MorseKOB/MuKOB/hw/renderings/MK-CommAdapter_1_0_b.png

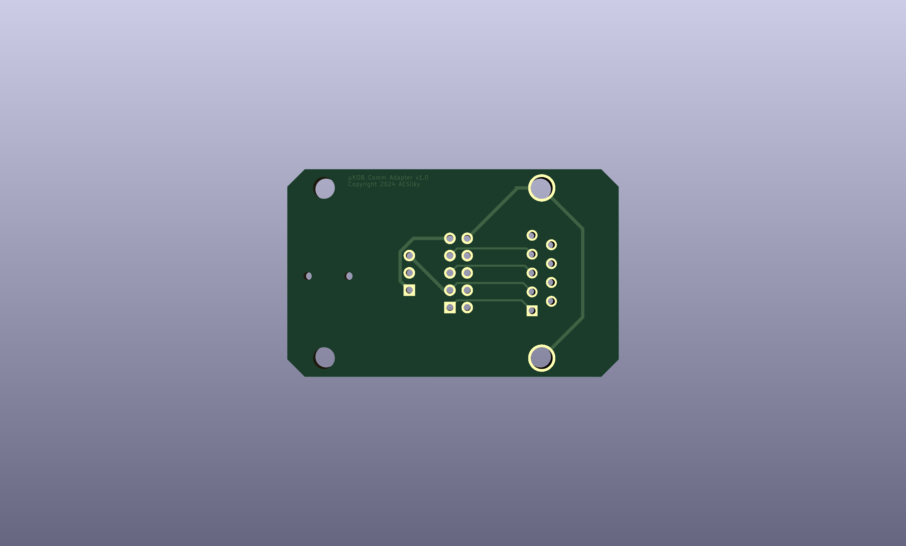
hw/renderings/MK-CommAdapter_1_0_b.png
