MorseKOB/MuKOB/hw/renderings/MK-JackAdapter-v1_1.png

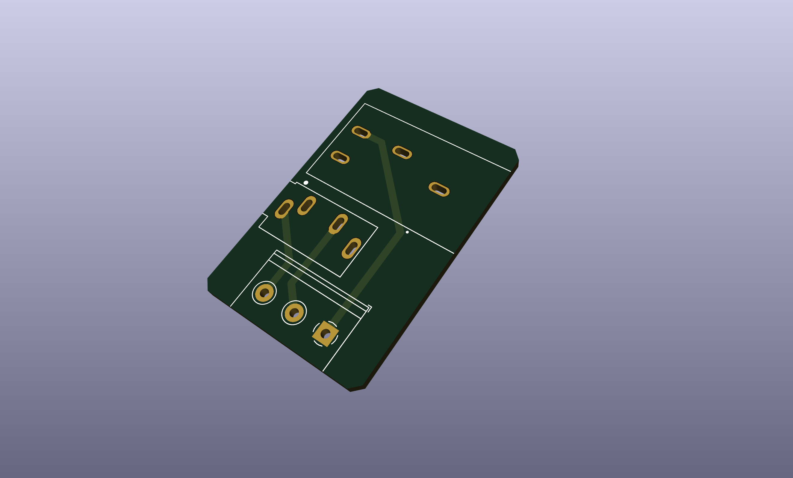
hw/renderings/MK-JackAdapter-v1_1.png
