MorseKOB/MuKOB/hw/renderings/MK-JackAdapter_1_0_b.png

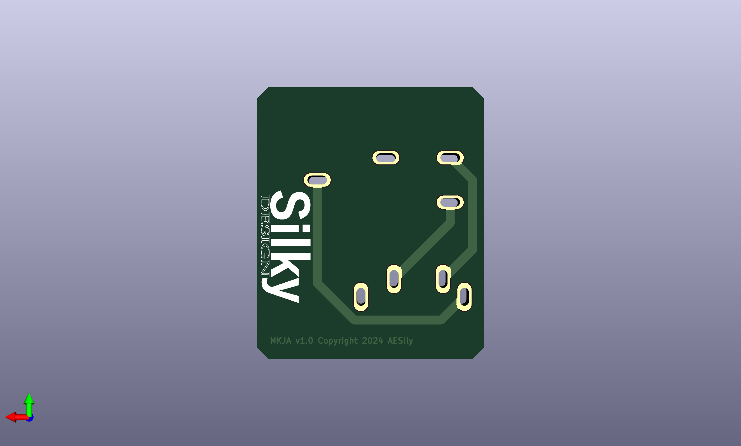
hw/renderings/MK-JackAdapter_1_0_b.png
