MorseKOB/MuKOB/hw/renderings/MK-KS-MkII_1_0_b.png

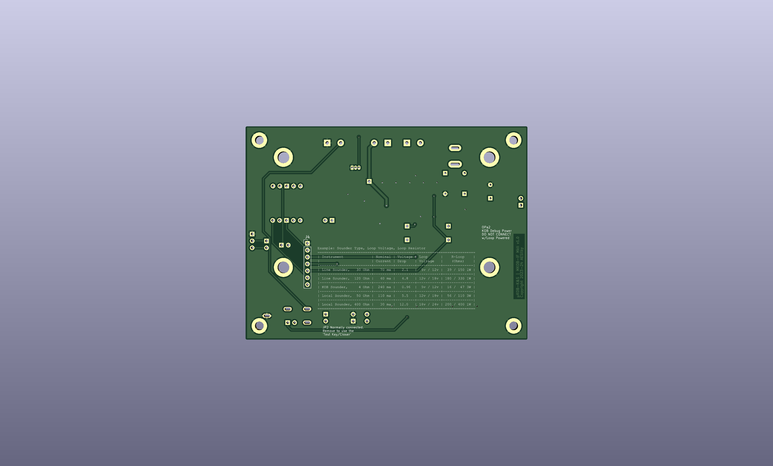
hw/renderings/MK-KS-MkII_1_0_b.png
