MorseKOB/MuKOB/hw/renderings/MuKOB_1_0_b.png

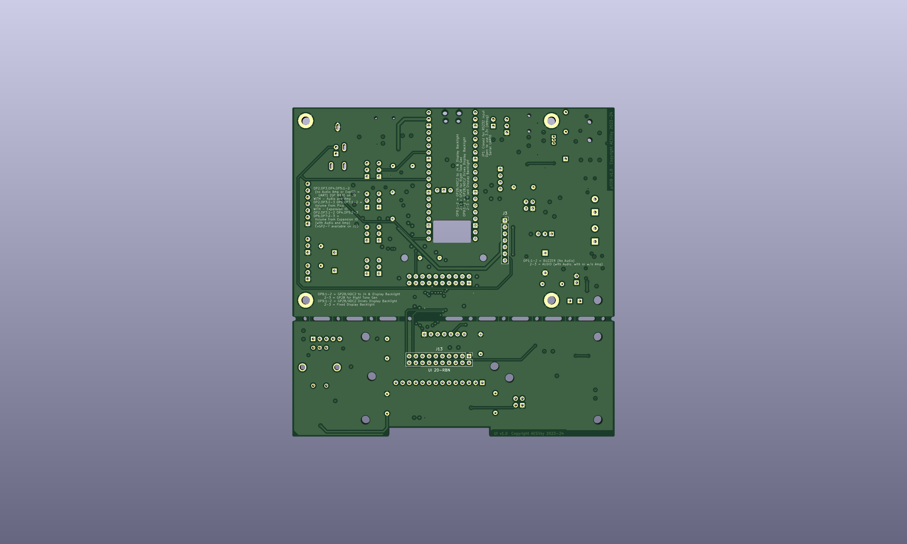
hw/renderings/MuKOB_1_0_b.png
