MorseKOB/MuKOB/hw/renderings/MuKOB_1_0_f.png

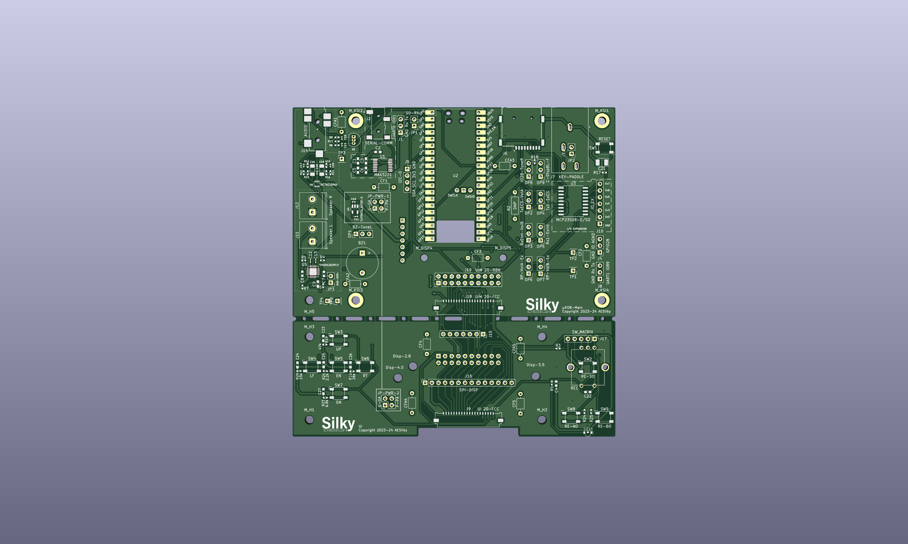
hw/renderings/MuKOB_1_0_f.png
