MorseKOB/MuKOB/component-docs/FFC_FPC-SOCK-Amphenol-F52R-mech.pdf

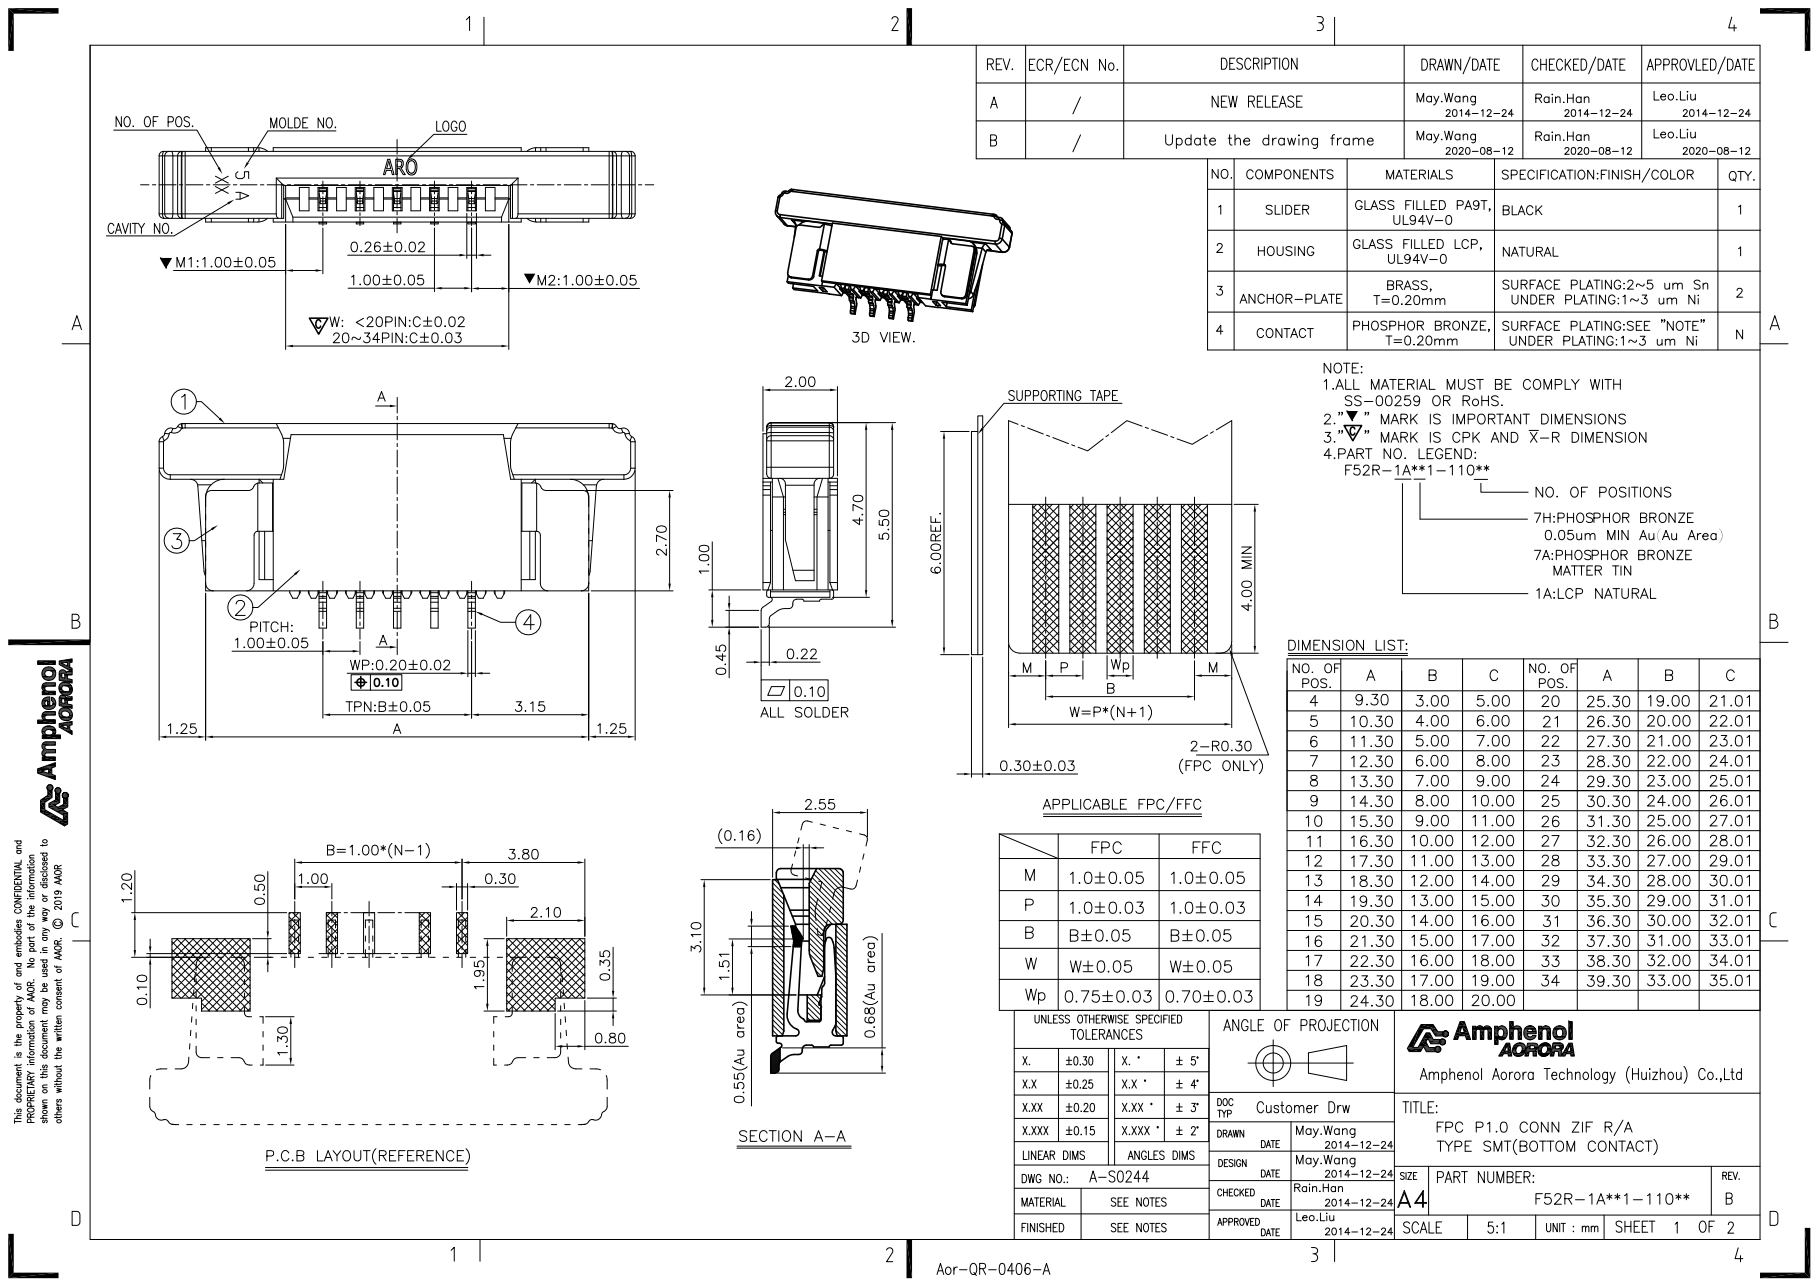
[picture p38: page 1]

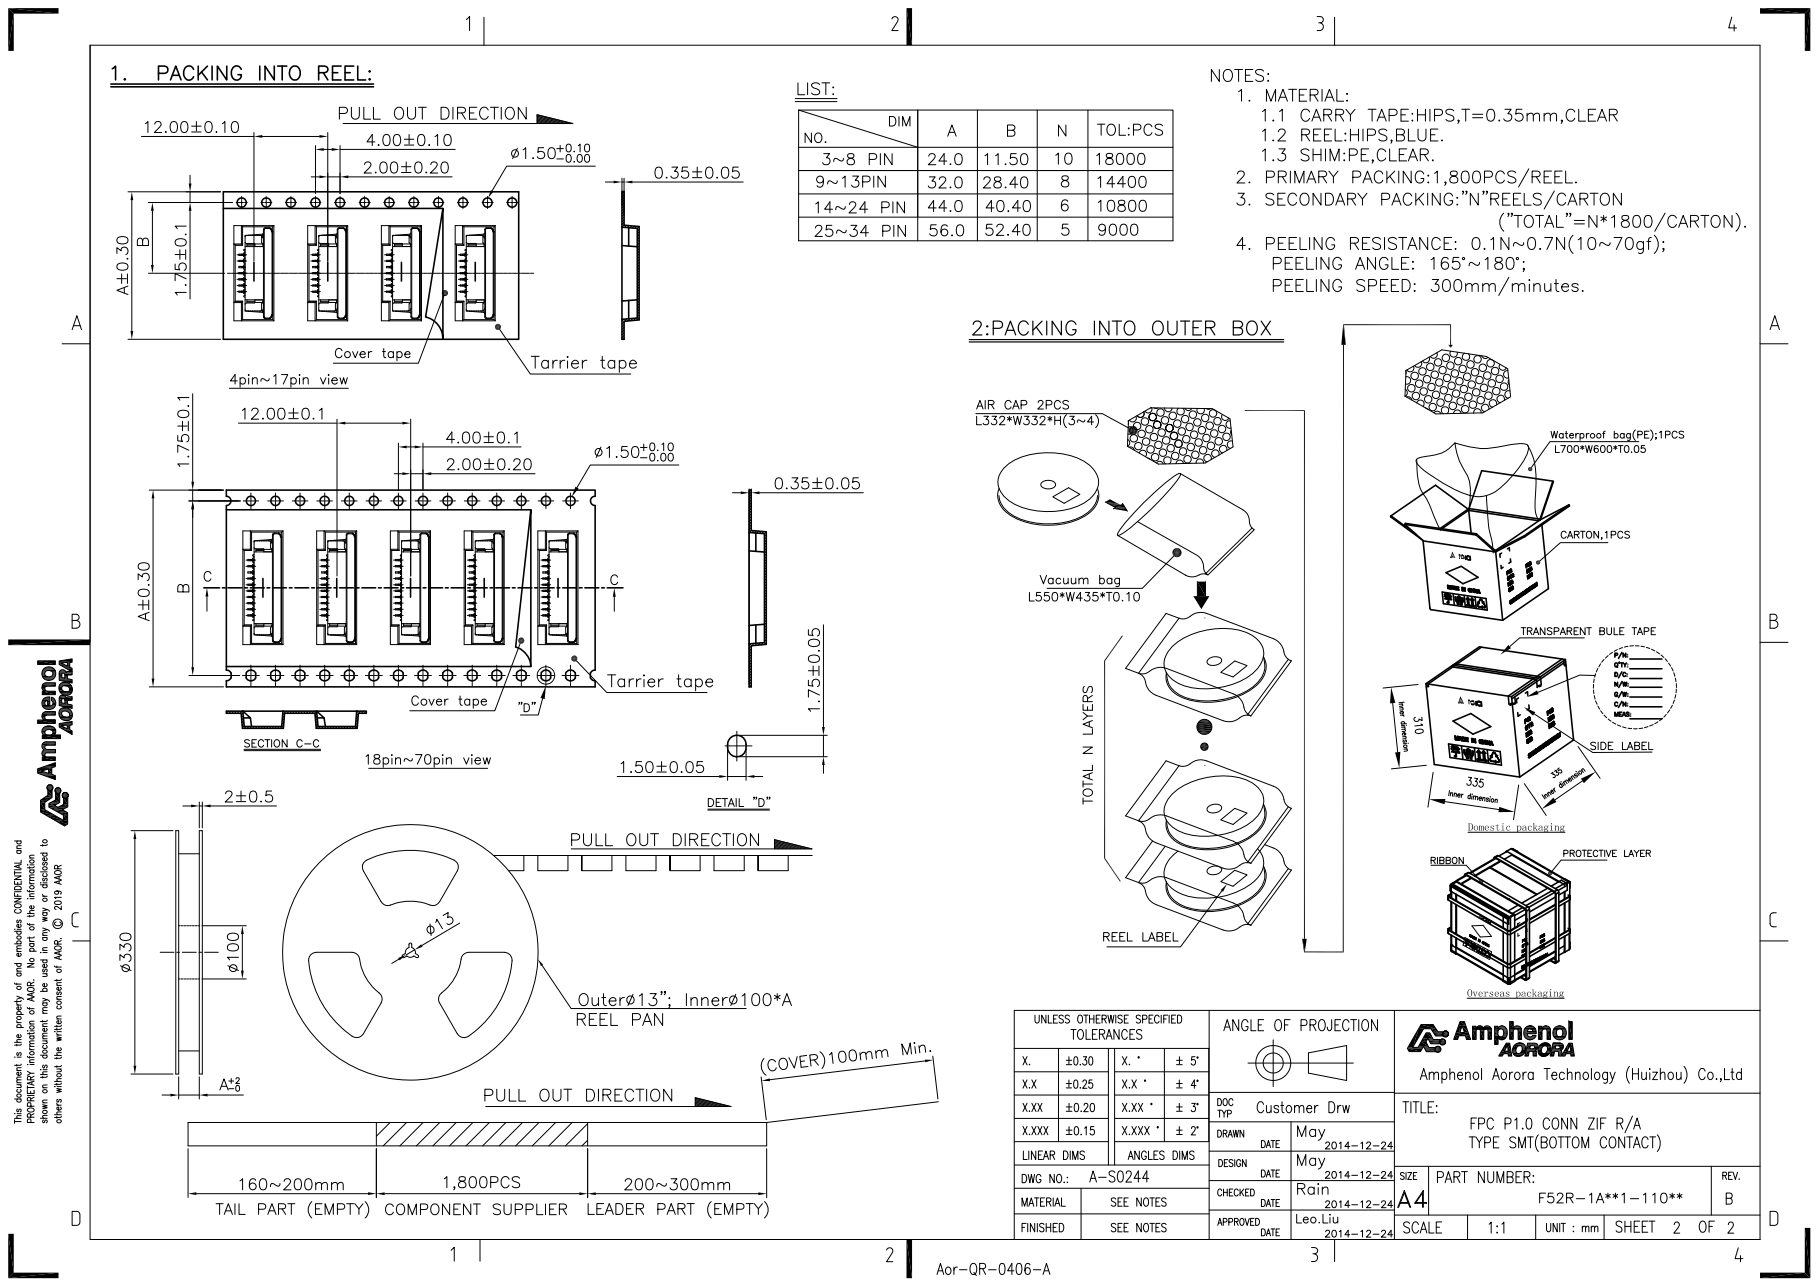
[picture p39: page 2]
