MorseKOB/MuKOB/component-docs/FFC_FPC-SOCK-RA-Amphenol-f51w_f51z_f514_f536-mech.pdf

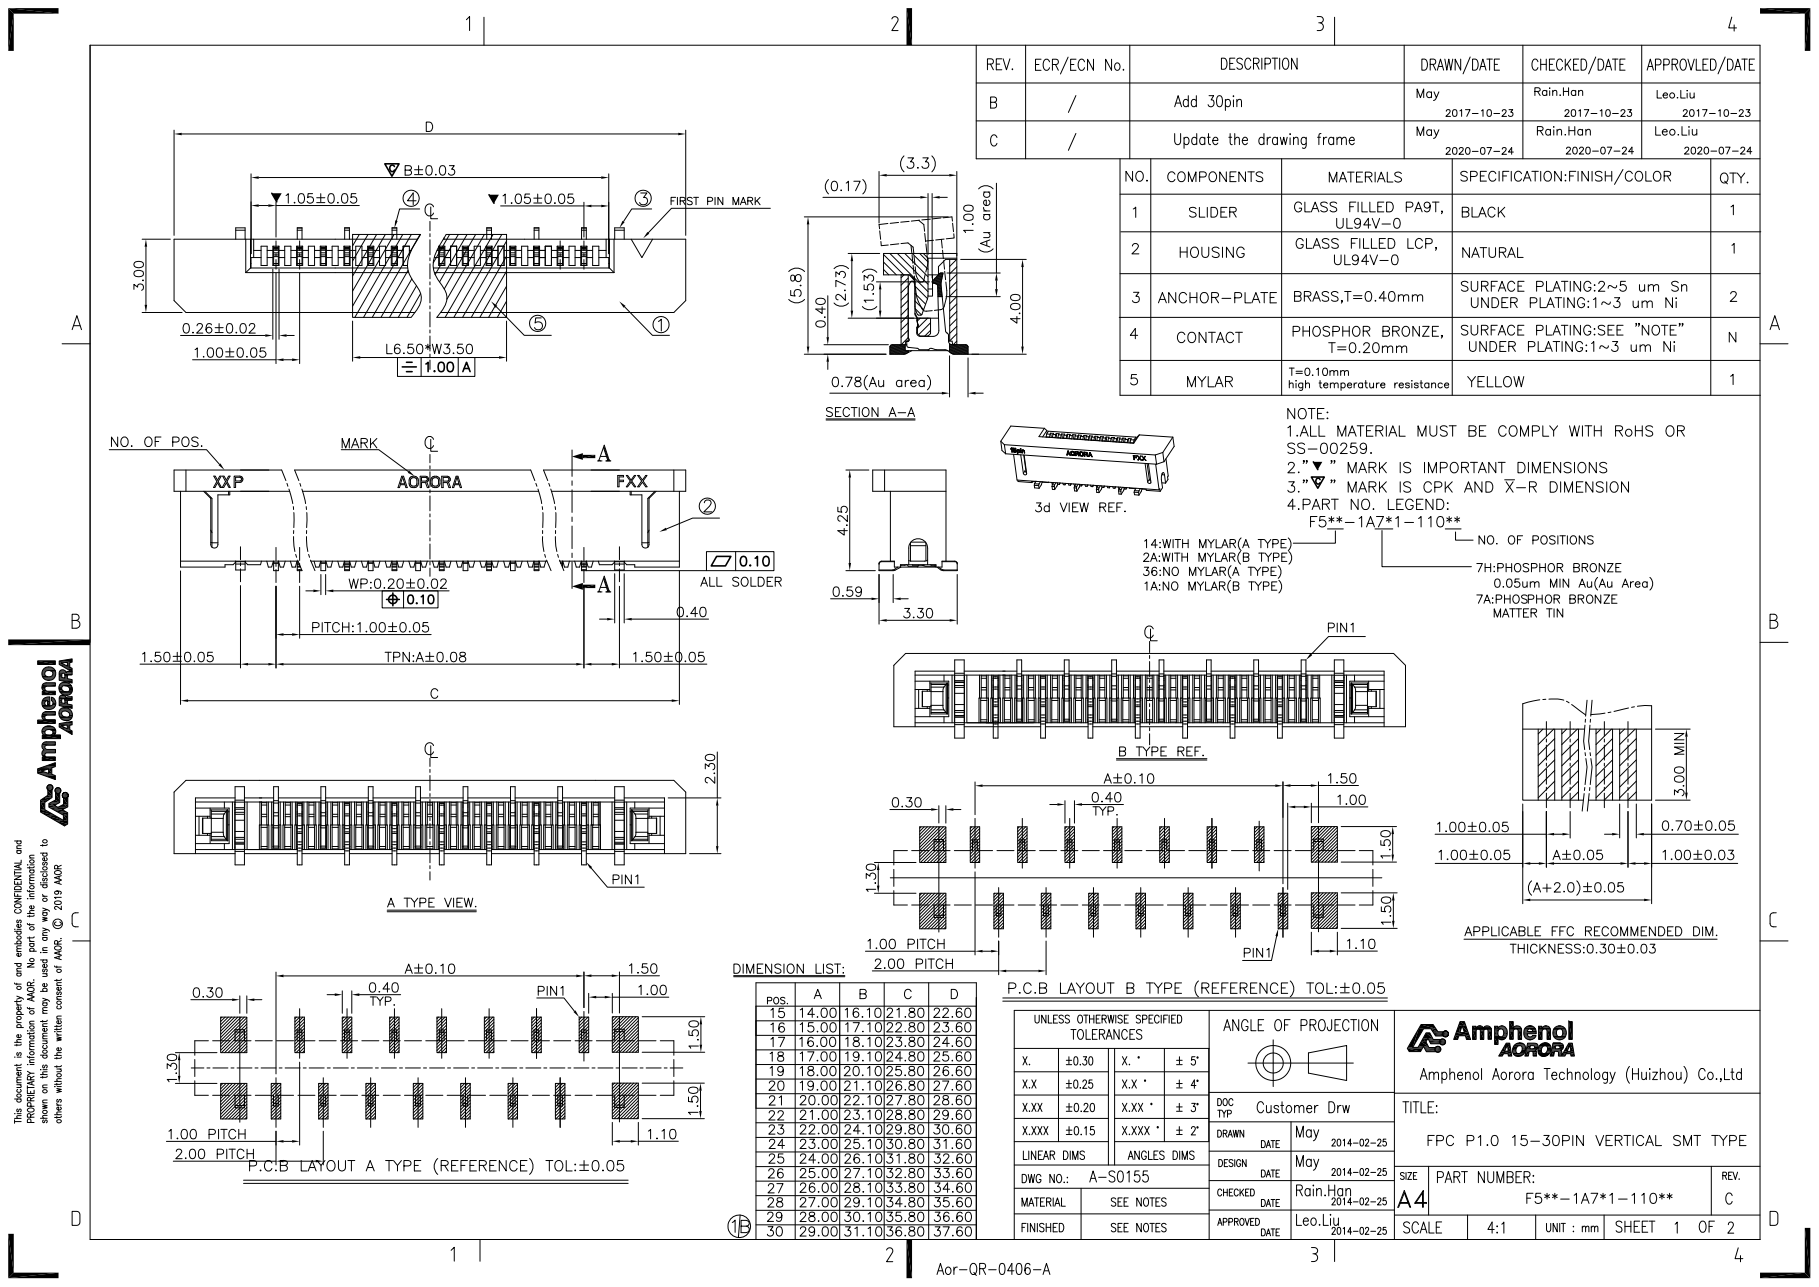
[picture p40: page 1]

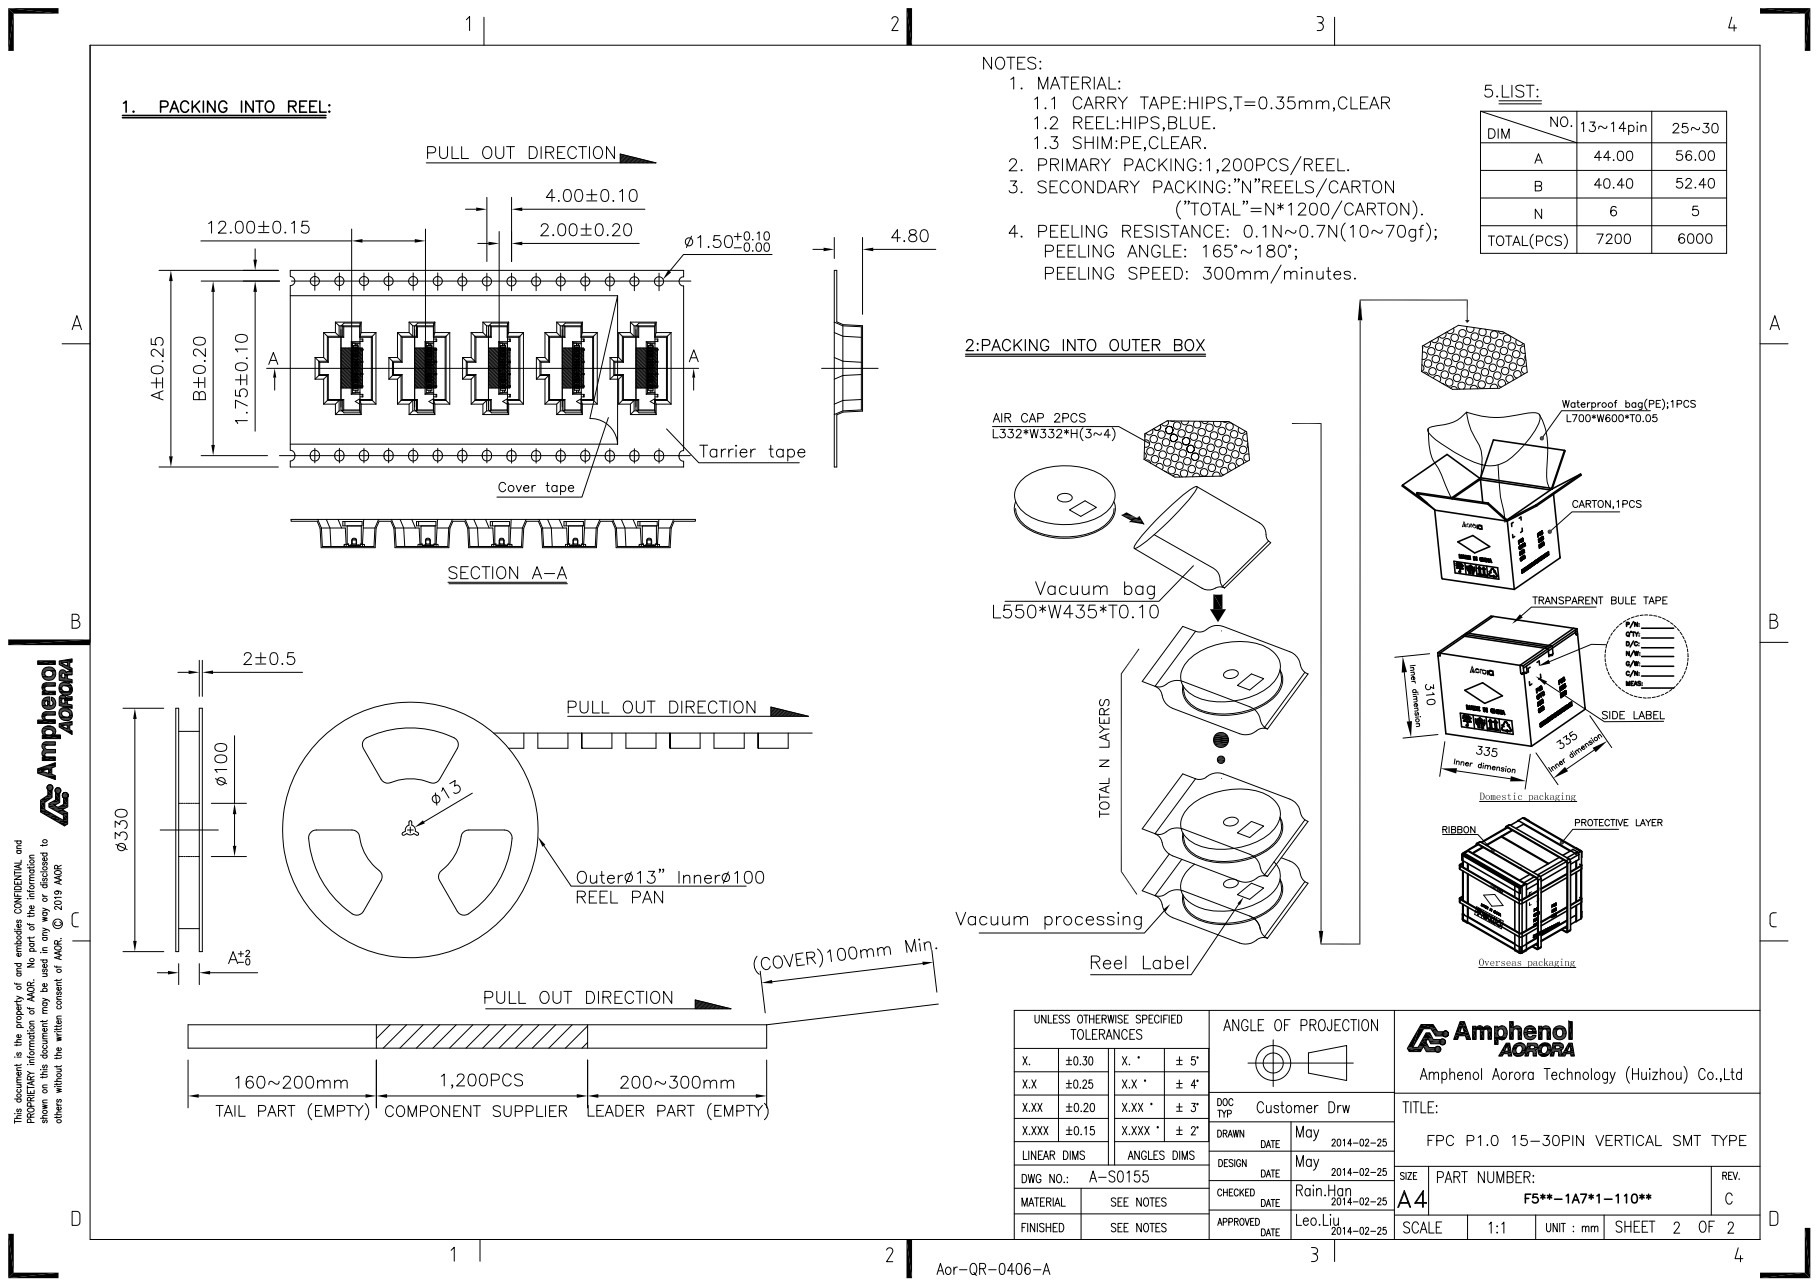
[picture p41: page 2]
