MorseKOB/MuKOB/hw/schematics/MK-CommAdapter_1_0.pdf

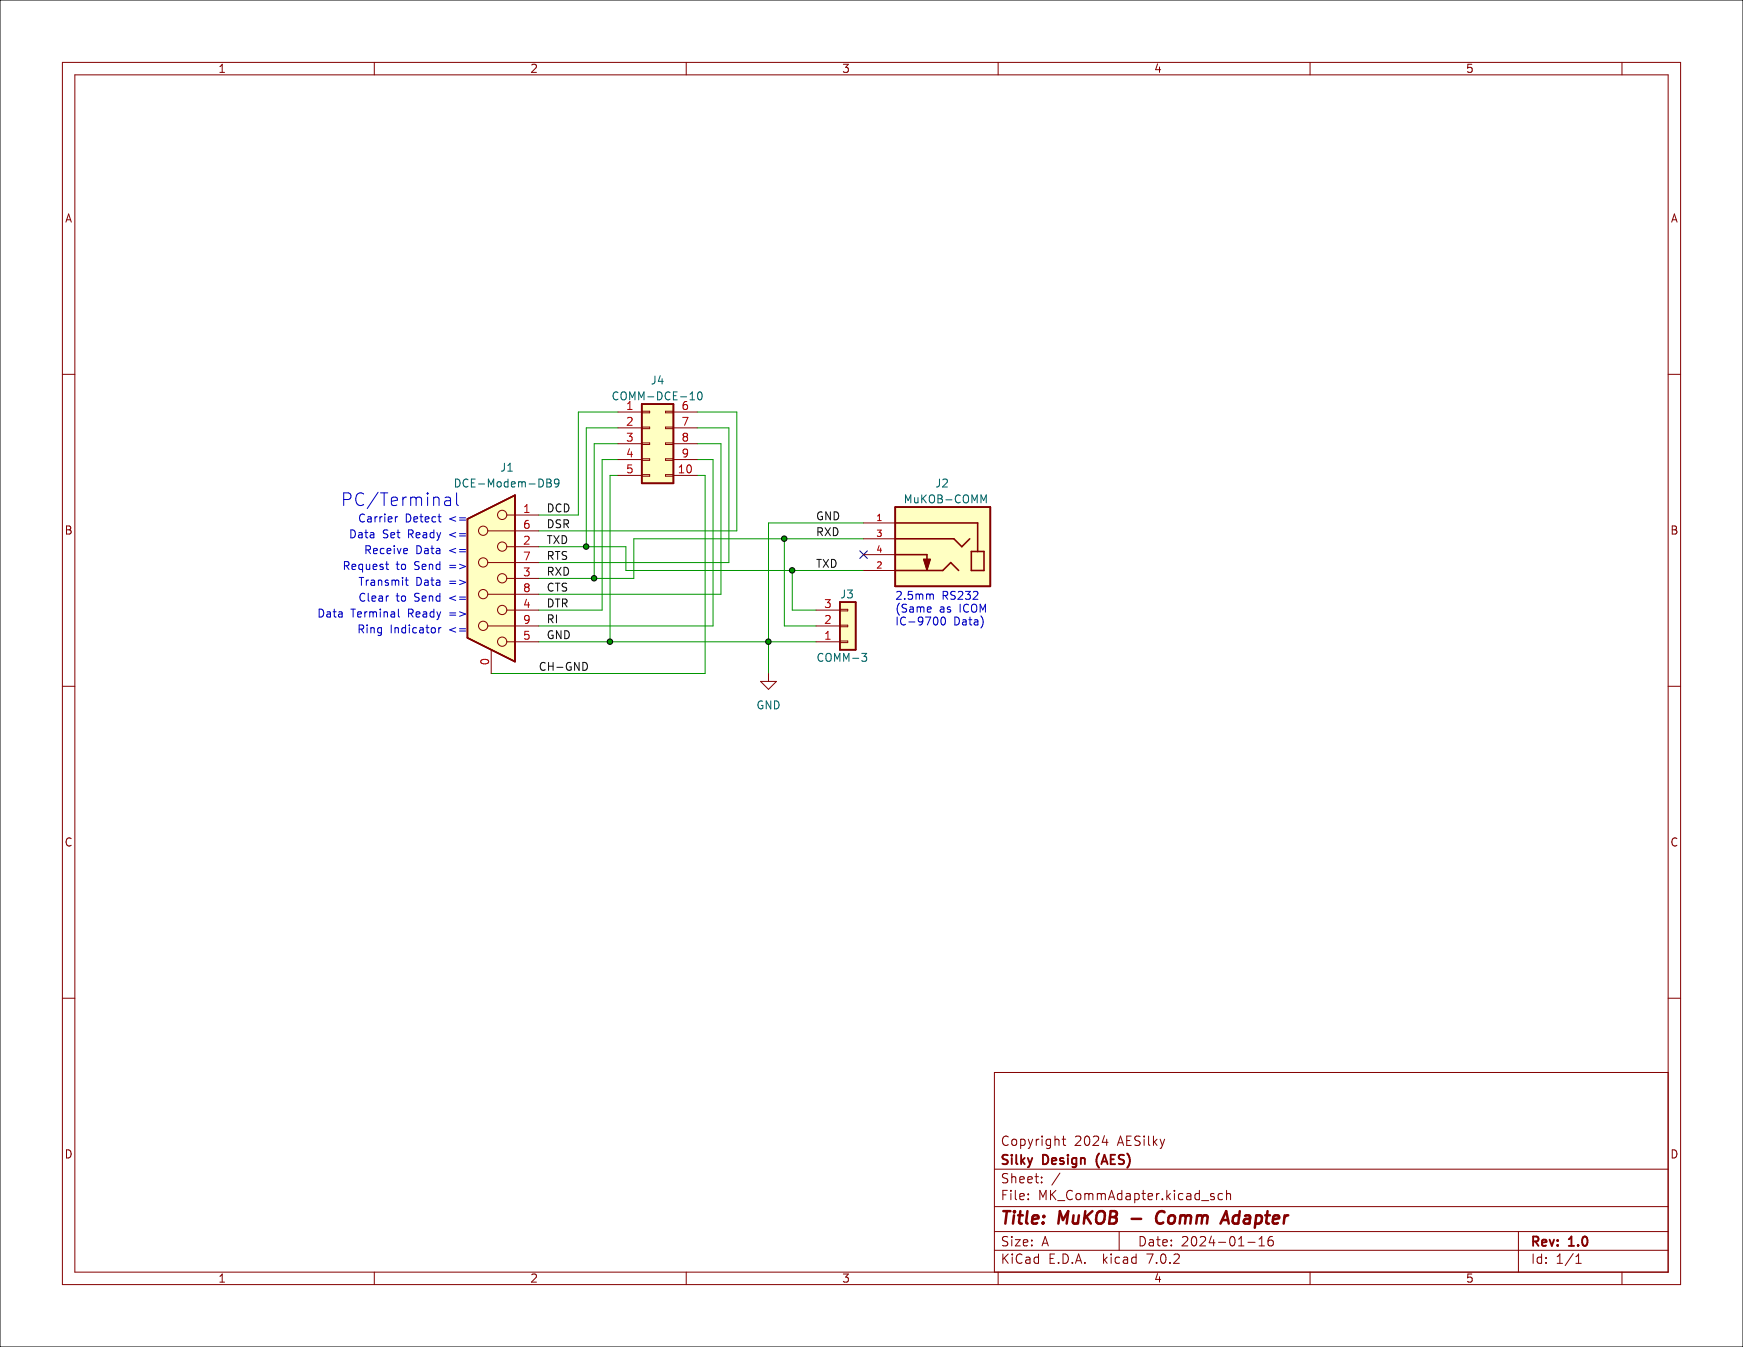
[picture p42: page 1]
