MorseKOB/MuKOB/hw/schematics/MK-JackAdapter_1_0.pdf

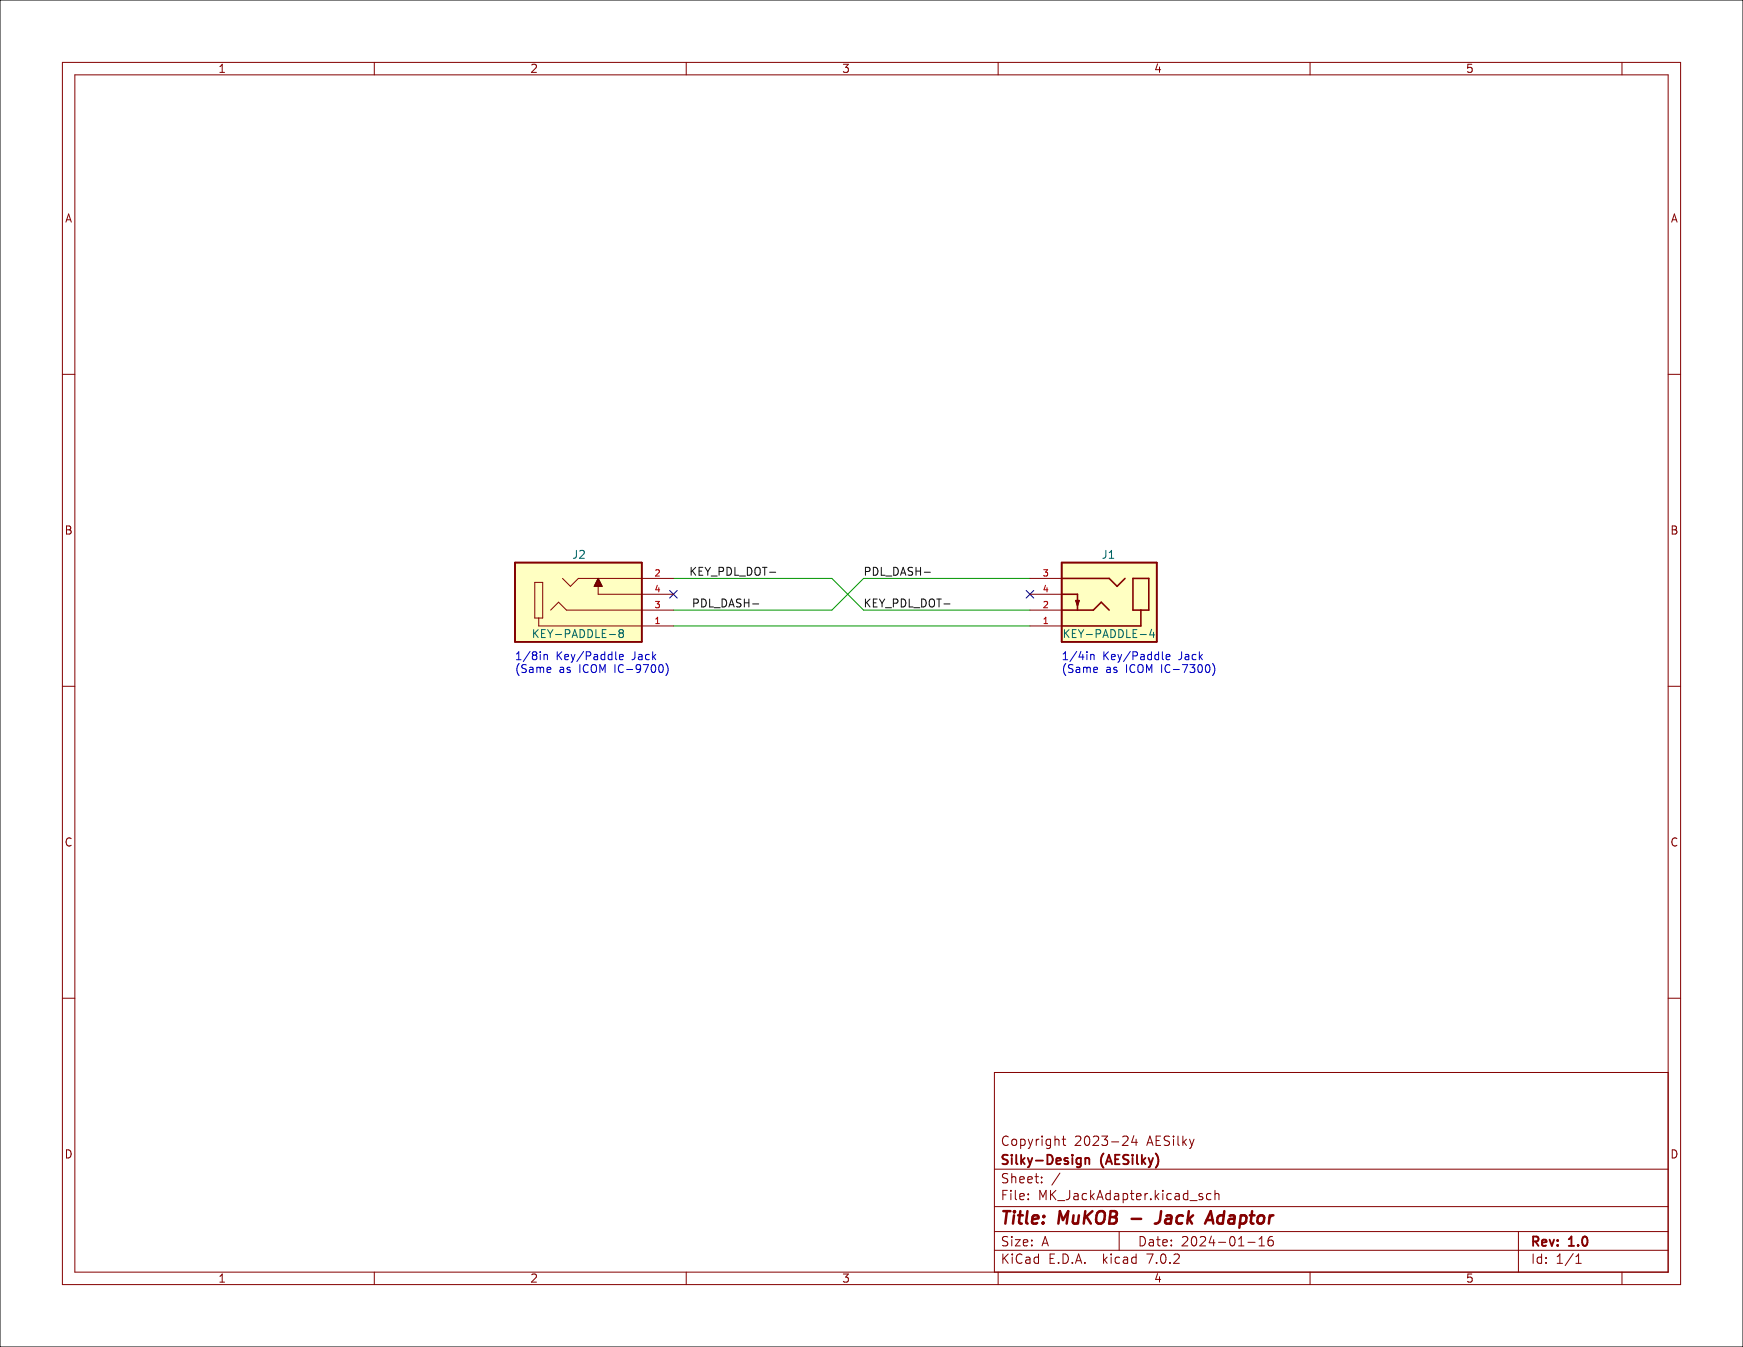
[picture p43: page 1]
