MorseKOB/MuKOB/hw/schematics/MK-KS-MkII_1_0.pdf

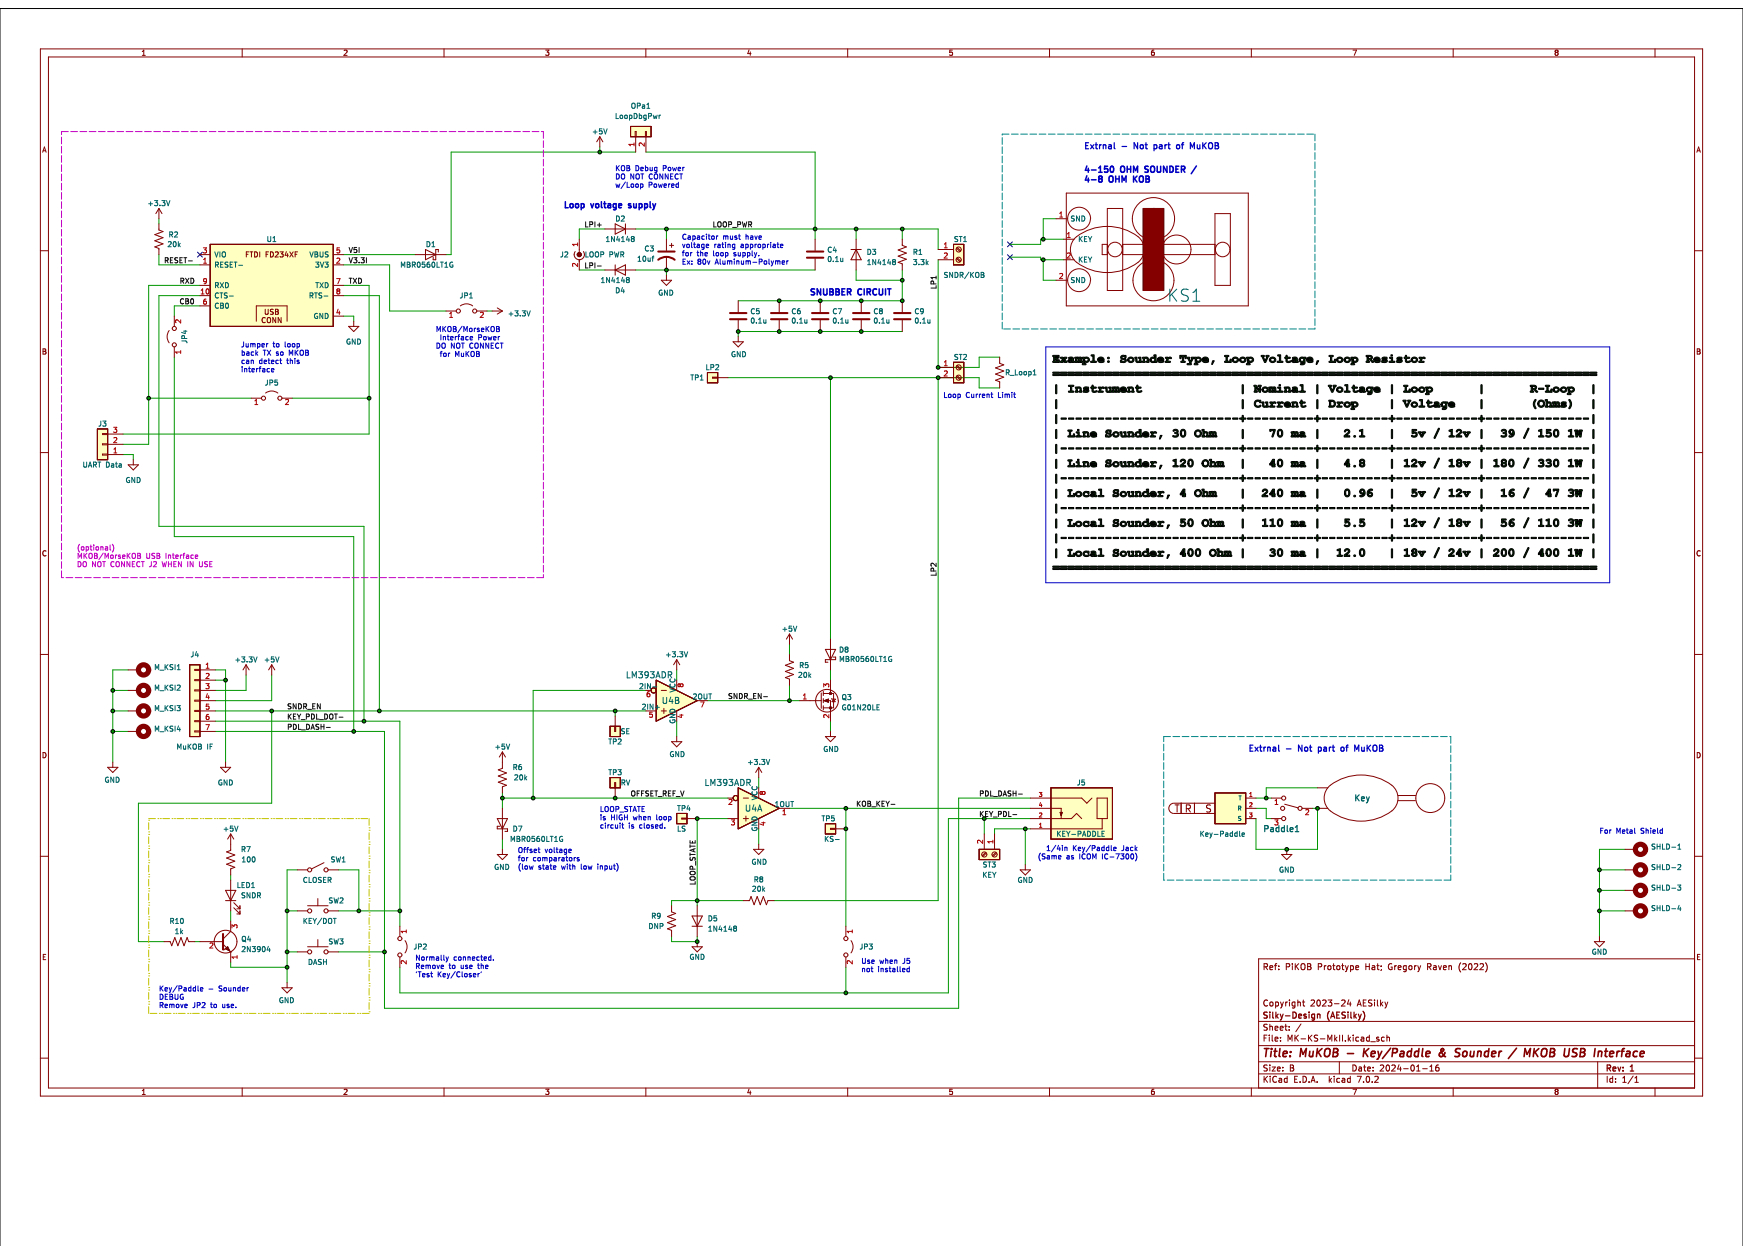
[picture p44: page 1]
