MorseKOB/MuKOB/hw/schematics/MK-KS_1_0.pdf

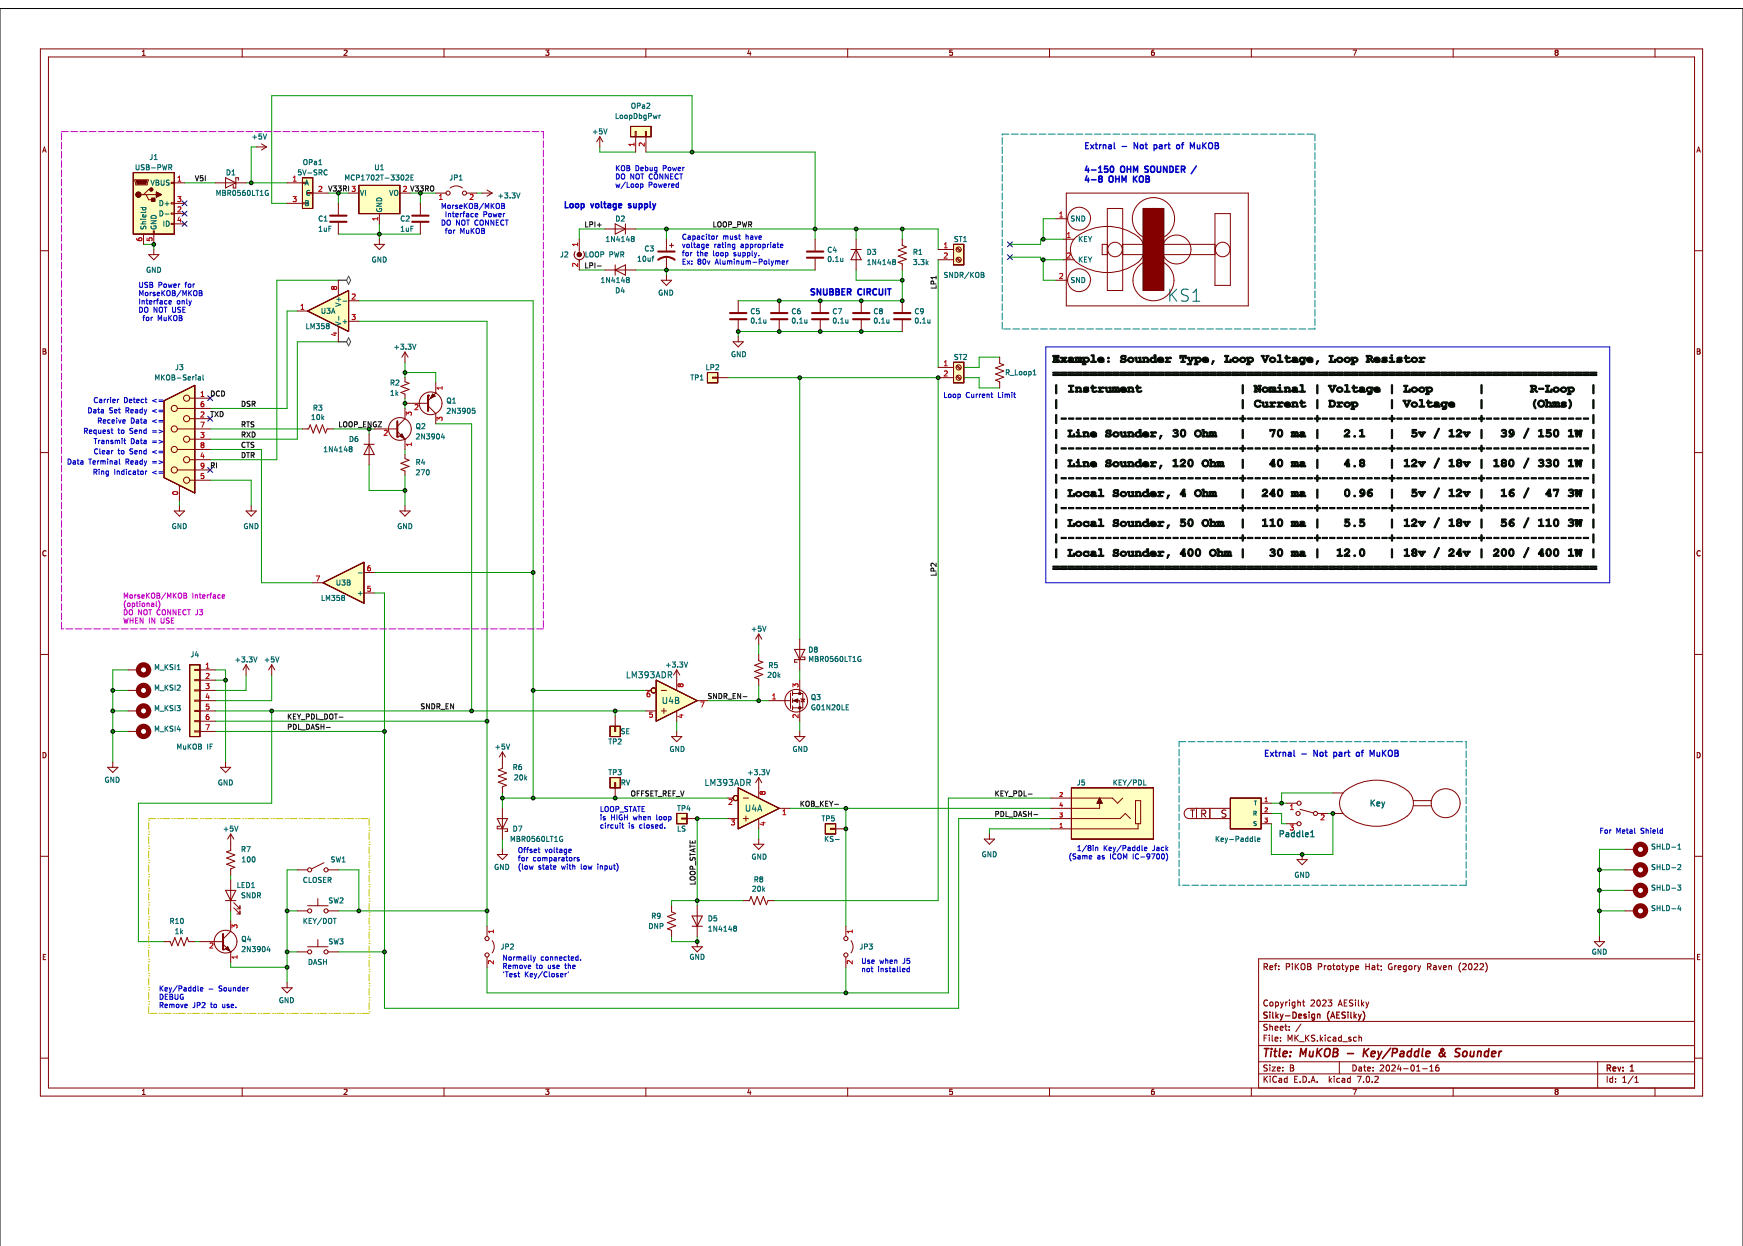
[picture p45: page 1]
