MorseKOB/MuKOB/hw/schematics/MuKOB_1_0.pdf

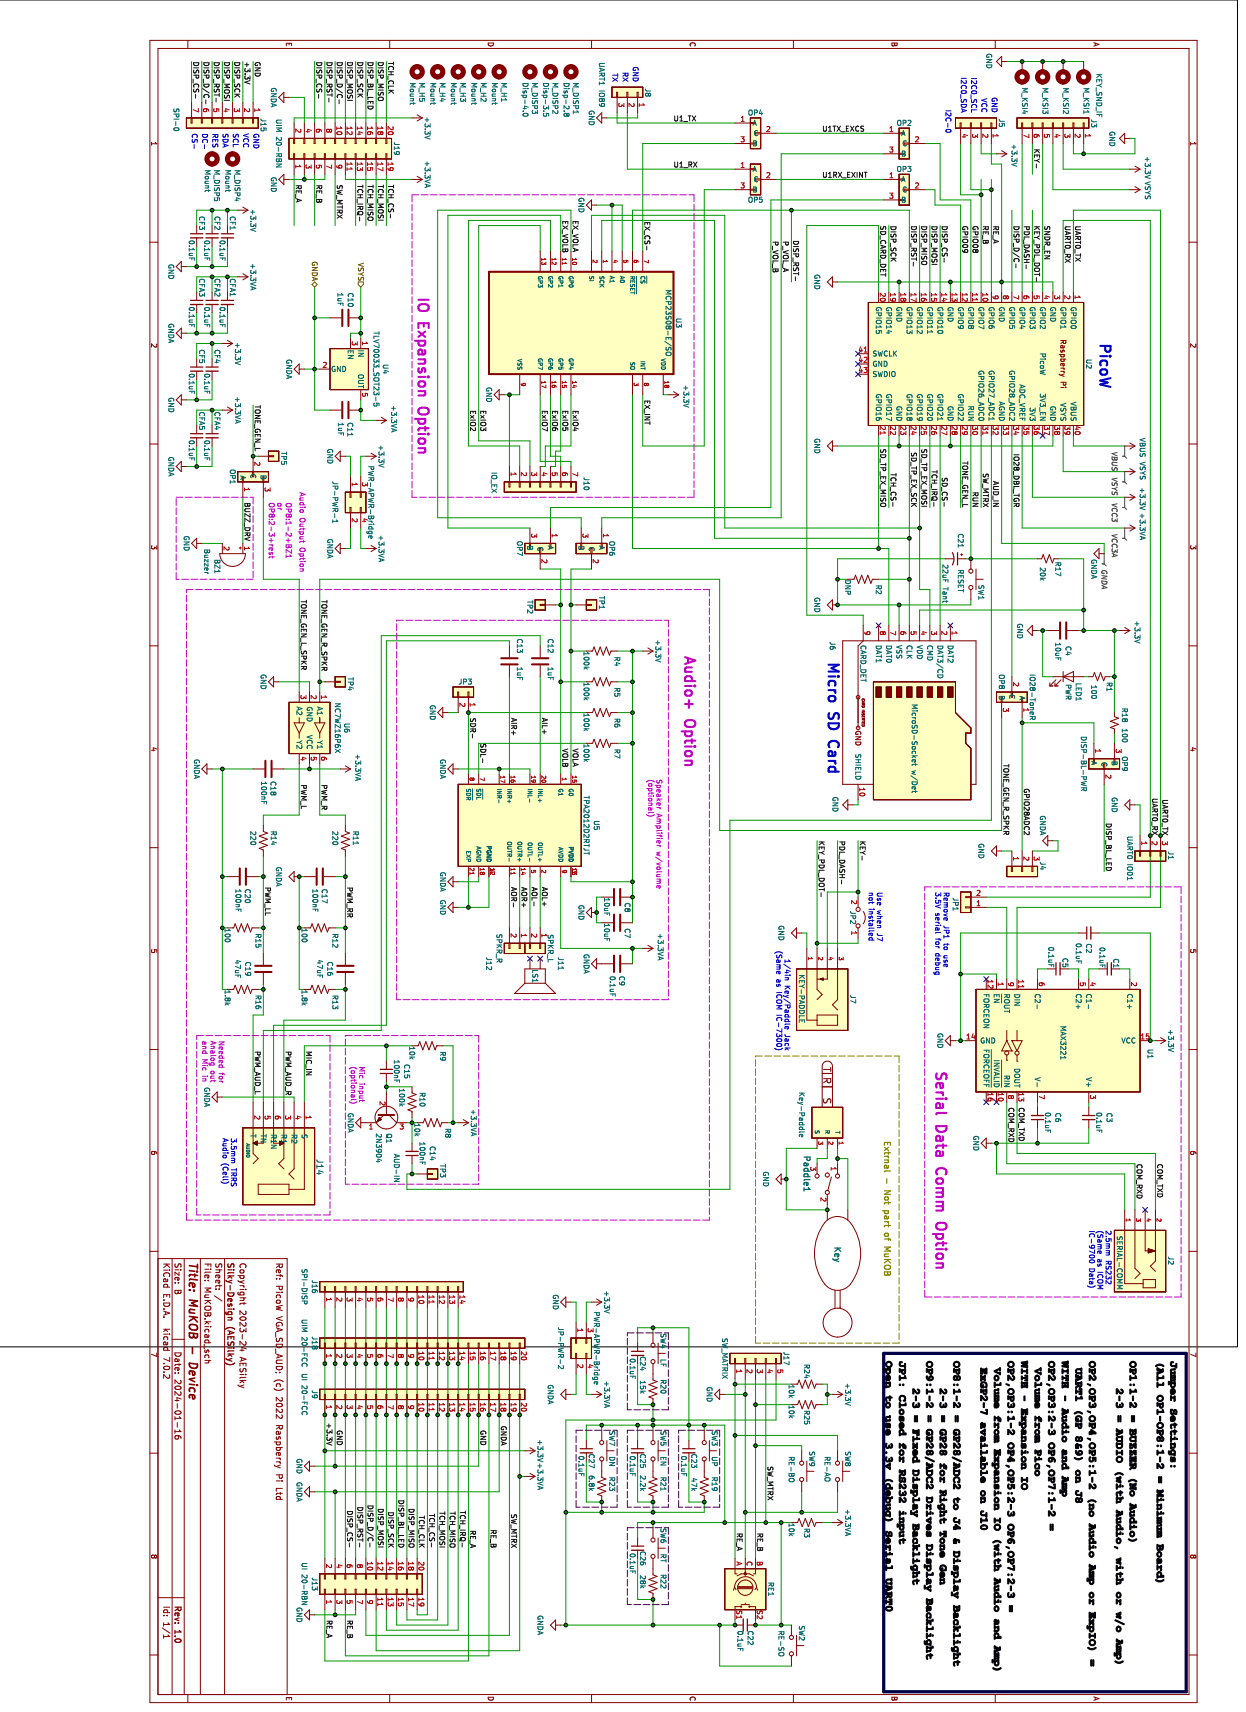
[picture p46: page 1]
