MorseKOB/MuKOB/src/mkdebug.h

/**
 * MuKOB Debugging flags and utilities.
 *
 * Copyright 2023 AESilky
 * SPDX-License-Identifier: MIT License
 */
#ifndef _MKDEBUG_H_
#define _MKDEBUG_H_
#ifdef __cplusplus
extern "C" {
#endif

#include "cmd_t.h" // Command processing type definitions

#include "stdbool.h"
#include "stdint.h"

extern volatile uint16_t debugging_flags;
#define DEBUGGING_MORSE_DECODE 0x0001
#define DEBUGGING_MORSE_DECODE_SKIP 0x0002

extern const cmd_handler_entry_t cmd_mkdebug_entry;

/**
 * @brief Board level debug flag that can be changed by code.
 * @ingroup debug
 *
 * @return Debug flag state
 */
extern bool mk_debug();

/**
 * @brief Set the state of the board level debug flag.
 *        If changed, MSG_DEBUG_CHG will be posted if the message system is initialized.
 * @ingroup debug
 *
 * @param debug The new state
 * @return true If the state changed.
 */
extern bool mk_debug_set(bool debug);

#ifdef __cplusplus
}
#endif
#endif // _MKDEBUG_H_
