MorseKOB/MuKOB/src/ui/cmd/cmd.c

/**
 * MuKOB CMD Command shell - On the terminal.
 *
 * Copyright 2023 AESilky
 * SPDX-License-Identifier: MIT License
 *
 */

#include "cmd.h"
#include "system_defs.h"

#include "config.h"
#include "cmt.h"
#include "mkdebug.h"
#include "mkwire.h"
#include "morse.h"
#include "term.h"
#include "ui_term.h"
#include "util.h"
#include "pico/printf.h"

#include <string.h>

#define CMD_LINE_MAX_ARGS 64

// Buffer to copy the input line into to be parsed.
static char _cmdline_parsed[UI_TERM_GETLINE_MAX_LEN_];

// Command processor declarations
static int _cmd_connect(int argc, char** argv, const char* unparsed);
static int _cmd_encode(int argc, char** argv, const char* unparsed);
static int _cmd_help(int argc, char** argv, const char* unparsed);
static int _cmd_keys(int argc, char** argv, const char* unparsed);
static int _cmd_proc_status(int argc, char** argv, const char* unparsed);
static int _cmd_speed(int argc, char** argv, const char* unparsed);
static int _cmd_wire(int argc, char** argv, const char* unparsed);

// Command processors framework
static const cmd_handler_entry_t _cmd_connect_entry = {
    _cmd_connect,
    1,
    "connect",
    "[wire-number]",
    "Connect/disconnect (toggle) the current wire. Connect to a specific wire.",
};
static const cmd_handler_entry_t _cmd_encode_entry = {
    _cmd_encode,
    1,
    "encode",
    "<string-to-encode>",
    "Encode a string to Morse.",
};
static const cmd_handler_entry_t _cmd_help_entry = {
    _cmd_help,
    1,
    "help",
    "[-a|--all] [command_name [command_name...]]",
    "List of commands or information for a specific command(s).\n  -a|--all : Display hidden commands.\n",
};
static const cmd_handler_entry_t _cmd_keys_entry = {
    _cmd_keys,
    4,
    "keys",
    "",
    "List of the keyboard control key actions.\n",
};
static const cmd_handler_entry_t _cmd_proc_status_entry = {
    _cmd_proc_status,
    3,
    ".ps",
    "",
    "Display process status per second.\n",
};
static const cmd_handler_entry_t _cmd_speed_entry = {
    _cmd_speed,
    1,
    "speed",
    "[text-speed] [character-speed]",
    "Display or set the 'Text' and 'Character' speeds.",
};
static const cmd_handler_entry_t _cmd_wire_entry = {
    _cmd_wire,
    1,
    "wire",
    "[wire-number]",
    "Display the current wire. Set the wire number.",
};

/**
 * @brief List of Command Handlers
 */
static const cmd_handler_entry_t* _command_entries[] = {
    & cmd_mkdebug_entry,        // .debug - 'DOT' commands come first
    & _cmd_proc_status_entry,   // .ps
    & cmd_bootcfg_entry,
    & cmd_cfg_entry,
    & cmd_configure_entry,
    & _cmd_connect_entry,
    & _cmd_encode_entry,
    & _cmd_help_entry,
    & _cmd_keys_entry,
    & cmd_load_entry,
    & cmd_save_entry,
    & _cmd_speed_entry,
    & cmd_station_entry,
    & _cmd_wire_entry,
    ((cmd_handler_entry_t*)0),  // Last entry must be a NULL
};


// Internal (non-command) declarations

static void _hook_keypress();

// Class data

static cmd_state_t _cmd_state = CMD_SNOOZING;
//static term_color_pair_t _scr_color_save;
//static scr_position_t _scr_cursor_position_save;


// Command functions

static int _cmd_connect(int argc, char** argv, const char* unparsed) {
    if (argc > 2) {
        cmd_help_display(&_cmd_connect_entry, HELP_DISP_USAGE);
        return (-1);
    }
    int16_t current_wire = mkwire_wire_get();
    if (argc == 2) {
        bool success;
        uint16_t wire = (uint16_t)uint_from_str(argv[1], &success);
        if (!success) {
            ui_term_printf("Value error - '%s' is not a number.\n", argv[1]);
            return (-1);
        }
        if (wire < 1 || wire > 999) {
            ui_term_puts("Wire number must be 1 to 999.\n");
            return (-1);
        }
        if (wire != current_wire) {
            // The wire specified is not the current wire - connect to it.
            ui_term_printf("Connecting to wire %hu...\n", wire);
            cmt_msg_t msg;
            msg.id = MSG_WIRE_CONNECT;
            msg.data.wire = wire;
            postBEMsgBlocking(&msg);
            return (0);
        }
    }
    char* op = (mkwire_is_connected() ? "Disconnecting from" : "Connecting to");
    ui_term_printf("%s wire %hu...\n", op, current_wire);
    cmt_msg_t msg;
    msg.id = MSG_WIRE_CONNECT_TOGGLE;
    postBEMsgBlocking(&msg);
    return (0);
}

static int _cmd_encode(int argc, char** argv, const char* unparsed) {
    if (argc < 2) {
        cmd_help_display(&_cmd_encode_entry, HELP_DISP_USAGE);
        return (-1);
    }
    cmt_msg_t msg;
    mcode_seq_t* mcode_space;
    for (int i = 1; i < argc; i++) {
        char* str = argv[i];
        char c;
        while ('\000' != (c = *str++)) {
            mcode_seq_t* mcode_seq = morse_encode(c);
            // Post it to the backend to decode
            msg.id = MSG_MORSE_CODE_SEQUENCE;
            msg.data.mcode_seq = mcode_seq;
            postBEMsgBlocking(&msg);
        }
        if (i+1 < argc) {
            // Add a space
            mcode_space = morse_encode(' ');
            msg.id = MSG_MORSE_CODE_SEQUENCE;
            msg.data.mcode_seq = mcode_space;
            postBEMsgBlocking(&msg);
        }
    }

    return (0);
}

static int _cmd_help(int argc, char** argv, const char* unparsed) {
    const cmd_handler_entry_t** cmds;
    const cmd_handler_entry_t* cmd;
    bool disp_commands = true;
    bool disp_hidden = false;

    argv++;
    if (argc > 1) {
        // They entered an option and/or command names
        if (strcmp("-a", *argv) == 0 || strcmp("--all", *argv) == 0) {
            disp_hidden = true;
            argv++; argc--;
        }
    }
    if (argc > 1) {
        char* user_cmd;
        for (int i = 1; i < argc; i++) {
            cmds = _command_entries;
            user_cmd = *argv++;
            int user_cmd_len = strlen(user_cmd);
            while (NULL != (cmd = *cmds++)) {
                int cmd_name_len = strlen(cmd->name);
                if (user_cmd_len <= cmd_name_len && user_cmd_len >= cmd->min_match) {
                    if (0 == strncmp(cmd->name, user_cmd, user_cmd_len)) {
                        // This command matches
                        disp_commands = false;
                        cmd_help_display(cmd, HELP_DISP_LONG);
                        break;
                    }
                }
            }
            if (disp_commands) {
                ui_term_printf("Unknown: '%s'\n", user_cmd);
            }
        }
    }
    if (disp_commands) {
        // List all of the commands with thier usage.
        ui_term_puts("Commands:\n");
        cmds = _command_entries;
        while (NULL != (cmd = *cmds++)) {
            bool dot_cmd = ('.' == *(cmd->name));
            if (!dot_cmd || (dot_cmd && disp_hidden)) {
                cmd_help_display(cmd, HELP_DISP_NAME);
            }
        }
    }

    return (0);
}

static int _cmd_keys(int argc, char** argv, const char* unparsed) {
    if (argc > 1) {
        cmd_help_display(&_cmd_keys_entry, HELP_DISP_USAGE);
        return (-1);
    }
    ui_term_printf("':' : While connected, enters command mode for one command.\n");
    ui_term_printf("^H  : Backspace (same as Backspace key on most terminals).\n");
    ui_term_printf("^R  : Refresh the terminal screen.\n");
    ui_term_printf("^W  : Toggle the 'wire' connection (connect/disconnect).\n");
    ui_term_printf("ESC : Clear the input line.\n");

    return (0);
}

static void _cmd_ps_print(const proc_status_accum_t* ps, int corenum) {
    int uaf = ONE_SECOND_MS - (ps->t_active + ps->t_idle + ps->t_msgr);
    ui_term_printf("Core %d: Temp:%0.1f R:%hu I:%hu PT:%u IT:%u MRT:%u UAF:%d IS:0x%0.8x\n",
        corenum, ps->core_temp, ps->retrived, ps->idle, ps->t_active, ps->t_idle, ps->t_msgr, uaf, ps->int_status);
}

static int _cmd_proc_status(int argc, char** argv, const char* unparsed) {
    if (argc > 1) {
        cmd_help_display(&_cmd_proc_status_entry, HELP_DISP_USAGE);
    }
    proc_status_accum_t ps0, ps1;
    int smwc;
    cmt_proc_status_sec(&ps0, 0);
    cmt_proc_status_sec(&ps1, 1);
    smwc = cmt_sched_msg_waiting();
    _cmd_ps_print(&ps0, 0);
    _cmd_ps_print(&ps1, 1);
    ui_term_printf("Scheduled messages: %d\n", smwc);

    return (0);
}

static int _cmd_speed_get_value(const char* v) {
    bool success;
    uint8_t sp = (uint8_t)uint_from_str(v, &success);
    if (!success) {
        ui_term_printf("Value error - '%s' is not a number.\n", v);
        return (-1);
    }
    if (sp < 1 || sp > 99) {
        ui_term_puts("Speed must be 1 to 99.\n");
        return (-1);
    }
    return (sp);
}

static int _cmd_speed(int argc, char** argv, const char* unparsed) {
    if (argc > 3) {
        cmd_help_display(&_cmd_speed_entry, HELP_DISP_USAGE);
        return (-1);
    }
    config_t* cfg = config_current_for_modification();
    uint8_t char_sp = cfg->char_speed_min;
    uint8_t text_sp = cfg->text_speed;
    uint8_t new_char_sp = char_sp;
    uint8_t new_text_sp = text_sp;

    if (argc > 1) {
        // Speeds entered. First is 'text'
        new_text_sp = _cmd_speed_get_value(argv[1]);
        if (new_text_sp < 0) {
            return (-1);
        }
    }
    if (argc > 2) {
        // Speeds entered. Second is 'character'
        new_char_sp = _cmd_speed_get_value(argv[2]);
        if (new_char_sp < 0) {
            return (-1);
        }
        if (new_char_sp < new_text_sp) {
            ui_term_puts("Character speed must be >= Text speed. Setting equal.\n");
            new_char_sp = new_text_sp;
        }
    }
    ui_term_printf("Text speed: %hu  Character speed: %hu\n", new_text_sp, new_char_sp);
    if (new_text_sp != text_sp || new_char_sp != char_sp) {
        // Value(s) changed - set them both.
        cfg->text_speed = new_text_sp;
        cfg->char_speed_min = new_char_sp;
        config_indicate_changed();
    }
    return (0);
}

static int _cmd_wire(int argc, char** argv, const char* unparsed) {
    if (argc > 2) {
        cmd_help_display(&_cmd_wire_entry, HELP_DISP_USAGE);
        return (-1);
    }
    if (argc == 2) {
        bool success;
        uint16_t wire = (uint16_t)uint_from_str(argv[1], &success);
        if (!success) {
            ui_term_printf("Value error - '%s' is not a number.\n", argv[1]);
            return (-1);
        }
        if (wire < 1 || wire > 999) {
            ui_term_puts("Wire number must be 1 to 999.\n");
            return (-1);
        }
        config_t* cfg = config_current_for_modification();
        if (wire != cfg->wire) {
            cfg->wire = wire;
            config_indicate_changed();
        }
    }
    else {
        ui_term_printf("Wire: %hd\n", mkwire_wire_get());
    }
    return (0);
}

// Internal functions

/**
 * @brief Registered to handle ^C to toggle the connect/disconnect.
 * @ingroup ui
 *
 * @param c Should be ^C
 */
void _handle_connect_toggle_char(char c) {
    // ^C can be typed to connect/disconnect.
    cmt_msg_t msg;
    msg.id = MSG_WIRE_CONNECT_TOGGLE;
    postBEMsgBlocking(&msg);
}

/**
 * @brief Registered to handle ^R to re-initialize the terminal.
 *
 * @param c Should be ^R
 */
void _handle_reinit_terminal_char(char c) {
    // ^R can be typed if the terminal gets messed up or is connected after MuKOB has started.
    // This re-initializes the terminal.
    cmt_msg_t msg;
    msg.id = MSG_CMD_INIT_TERMINAL;
    msg.data.c = c;
    postUIMsgBlocking(&msg);
}

void _notified_of_keypress() {
    // A character is available from the terminal. Getting called clears the registration.
    //
    // See if it's our wakeup char. If so, post a message to kick off our command processing.
    // If not, throw it away.
    int ci = term_getc();
    while (ci >= 0) {
        char c = (char)ci;
        if (CMD_WAKEUP_CHAR == c) {
            // Post a message to our loop with the character if we can read one (should be able to).
            cmt_msg_t msg;
            msg.id = MSG_CMD_KEY_PRESSED;
            msg.data.c = c;
            postUIMsgBlocking(&msg);
            // We don't re-register, as something else handles the incoming chars until we go idle again.
            return;
        }
        else {
            ui_term_handle_control_character(c); // This might not be a control char, but that's okay.
        }
        // If it's not our wake char, read again. When no chars are ready, the call returns -1.
        ci = term_getc();
    }
    // If we get here we need to re-register so we are notified when another character is ready.
    _hook_keypress();
}

static void _hook_keypress() {
    // Look for our wakeup char being sent from the terminal.
    term_register_notify_on_input(_notified_of_keypress);
}

static void _process_line(char* line) {
    char* argv[CMD_LINE_MAX_ARGS];
    memset(argv, 0, sizeof(argv));

    _cmd_state = CMD_PROCESSING_LINE;

    ui_term_puts("\n");

    // Copy the line into a buffer for parsing
    strcpy(_cmdline_parsed, line);

    int argc = parse_line(_cmdline_parsed, argv, CMD_LINE_MAX_ARGS);
    char* user_cmd = argv[0];
    int user_cmd_len = strlen(user_cmd);
    bool command_matched = false;

    if (user_cmd_len > 0) {
        const cmd_handler_entry_t** cmds = _command_entries;
        const cmd_handler_entry_t* cmd;

        while (NULL != (cmd = *cmds++)) {
            int cmd_name_len = strlen(cmd->name);
            if (user_cmd_len <= cmd_name_len && user_cmd_len >= cmd->min_match) {
                if (0 == strncmp(cmd->name, user_cmd, user_cmd_len)) {
                    // This command matches
                    command_matched = true;
                    _cmd_state = CMD_EXECUTING_COMMAND;
                    cmd->cmd(argc, argv, line);
                    break;
                }
            }
        }
        if (!command_matched) {
            ui_term_printf("Command not found: '%s'. Try 'help'.\n", user_cmd);
        }
    }

    // If we aren't currently connected, get another line from the user.
    if (!mkwire_is_connected()) {
        // Get a command from the user...
        _cmd_state = CMD_COLLECTING_LINE;
        ui_term_printf("%c", CMD_PROMPT);
        ui_term_getline(_process_line);
    }
    else {
        cmd_enter_idle_state();
    }
}


// Public functions

void cmd_attn_handler(cmt_msg_t* msg) {
    // Called when MSG_CMD_KEY_PRESSED is received
    // We should be in a state where we are looking to be woken up
    // or building up a line to process.
    char c = msg->data.c;
    if (CMD_SNOOZING == _cmd_state) {
        // See if the char is 'wakeup'
        if (CMD_WAKEUP_CHAR == c) {
            // Wakeup received, change state to building line.
            _cmd_state = CMD_COLLECTING_LINE;
            term_cursor_moveto(ui_term_scroll_end_line_get(), 1);
            ui_term_use_cmd_color();
            putchar('\n');
            putchar(CMD_PROMPT);
            term_cursor_on(true);
            // Get a command from the user...
            ui_term_getline(_process_line);
        }
    }
}

/**
 * This is typically called by the UI when the system connects to a wire.
 */
extern void cmd_enter_idle_state() {
    if (CMD_SNOOZING != _cmd_state) {
        // Cancel any inprocess 'getline'
        ui_term_getline_cancel(_notified_of_keypress);
        // Put the terminal back to 'code' state
        term_cursor_on(false);
        ui_term_use_code_color();
        // go back to Snoozing
        _cmd_state = CMD_SNOOZING;
    }
}

const cmd_state_t cmd_get_state() {
    return _cmd_state;
}

void cmd_help_display(const cmd_handler_entry_t* cmd, const cmd_help_display_format_t type) {
    term_color_pair_t tc = ui_term_color_get();
    term_color_default();
    if (HELP_DISP_USAGE == type) {
        ui_term_puts("Usage: ");
    }
    int name_min = cmd->min_match;
    char* name_rest = ((cmd->name) + name_min);
    // Print the minimum required characters bold and the rest normal.
    term_text_bold();
    // ui_term_printf(format, cmd->name);
    ui_term_printf("%.*s", name_min, cmd->name);
    term_text_normal();
    // See if this is an alias for another command...
    bool alias = (CMD_ALIAS_INDICATOR == *cmd->usage);
    if (!alias) {
        ui_term_printf("%s %s\n", name_rest, cmd->usage);
        if (HELP_DISP_LONG == type || HELP_DISP_USAGE == type) {
            ui_term_printf("  %s\n", cmd->description);
        }
    }
    else {
        const char* aliased_for_name = ((cmd->usage) + 1);
        ui_term_printf("%s  Alias for: %s\n", name_rest, aliased_for_name);
        if (HELP_DISP_NAME != type) {
            // Find the aliased entry
            const cmd_handler_entry_t* aliased_cmd = NULL;
            const cmd_handler_entry_t* cmd_chk;
            const cmd_handler_entry_t** cmds = _command_entries;
            while (NULL != (cmd_chk = *cmds++)) {
                if (strcmp(cmd_chk->name, aliased_for_name) == 0) {
                    aliased_cmd = cmd_chk;
                    break;
                }
            }
            if (aliased_cmd) {
                // Put the terminal colors back, and call this again with the aliased command
                term_color_fg(tc.fg);
                term_color_bg(tc.bg);
                cmd_help_display(aliased_cmd, type);
            }
        }
    }
    term_color_fg(tc.fg);
    term_color_bg(tc.bg);
}

void cmd_module_init() {
    _cmd_state = CMD_SNOOZING;
    // Register the control character handlers.
    ui_term_register_control_char_handler(CMD_WIRE_CONNECT_TOGGLE_CHAR, _handle_connect_toggle_char);
    ui_term_register_control_char_handler(CMD_REINIT_TERM_CHAR, _handle_reinit_terminal_char);
    // Hook keypress looking for a ':' to wake us up.
    _hook_keypress();
}
