MorseKOB/MuKOB/src/ui/ui_term.c

/**
 * MuKOB User Interface - On the terminal.
 *
 * Copyright 2023 AESilky
 * SPDX-License-Identifier: MIT License
 *
*/
#include "ui_term.h"
#include "config.h"
#include "cmd.h"
#include "cmt.h"
#include "kob.h"
#include "term.h"
#include "util.h"
#include "hardware/rtc.h"
#include "pico/printf.h"
#include <ctype.h>
#include <string.h>

static const char* _current_sender;
static term_color_t _color_term_text_current_bg;
static term_color_t _color_term_text_current_fg;

static ui_term_control_char_handler _control_char_handler[32]; // Room for a handler for each control character

static char _getline_buf[UI_TERM_GETLINE_MAX_LEN_];
static int16_t _getline_index;

static bool _code_displaying;
static int _code_column;
static char _code_displayed[2 * UI_TERM_COLUMNS];

static kob_status_t _kob_status;

static uint16_t _scroll_end_line;
static uint16_t _station_list_separator_line;

static ui_term_input_available_handler _input_available_handler;
static ui_term_getline_callback_fn _getline_callback; // Function pointer to be called when an input line is ready

/**
 * @brief Message handler for `MSG_INPUT_CHAR_READY`
 * @ingroup ui
 *
 * @param msg Nothing important in the message.
 */
void _ui_term_handle_input_char_ready(cmt_msg_t* msg) {
    if (NULL != _input_available_handler) {
        _input_available_handler();
    }
}

/**
 * @brief A `term_notify_on_input_fn` handler for input ready.
 * @ingroup ui
 */
void _input_ready_hook(void) {
    // Since this is called by an interrupt handler,
    // post a UI message so that the input is handled
    // by the UI message loop.
    cmt_msg_t msg;
    msg.id = MSG_INPUT_CHAR_READY;
    postUIMsgBlocking(&msg);
    // The hook is cleared on notify, so hook ourself back in.
    term_register_notify_on_input(_input_ready_hook);
}

static void _draw_station_list_box(uint16_t lines) {
    uint16_t nsls = UI_TERM_STATION_LIST_LAST_LINE - (lines);
    // Save current cursor and set color
    term_cursor_save();
    term_set_origin_mode(TERM_OM_UPPER_LEFT);
    term_color_fg(UI_TERM_STATION_LIST_BOX_COLOR_FG);
    term_color_bg(UI_TERM_STATION_LIST_COLOR_BG);
    if (nsls > _station_list_separator_line && _station_list_separator_line > 0) {
        // Need to erase lines from old box
        term_cursor_moveto(_station_list_separator_line, 1);
        for (int i = 0; i <= (UI_TERM_STATION_LIST_LAST_LINE - _station_list_separator_line); i++) {
            term_erase_line();
            term_cursor_down_1();
        }
    }
    // Move to begining of separator line and set
    term_cursor_moveto(nsls, 1);
    // Draw the top
    term_charset(VT_100_LINEDRAW);
    for (int i = 0; i < UI_TERM_COLUMNS; i++) {
        if (i == (UI_TERM_COLUMNS / UI_TERM_STATIONS_PER_LINE) || i == ((((UI_TERM_COLUMNS / UI_TERM_STATIONS_PER_LINE) * 2) + 1))) {
            putchar(VT_LD_TCT);
        }
        else {
            putchar(VT_LD_HOR);
        }
    }
    // Draw the bars
    for (int i = nsls + 1; i <= nsls + lines; i++) {
        term_cursor_moveto(i, ((UI_TERM_COLUMNS / UI_TERM_STATIONS_PER_LINE) + 1));
        putchar(VT_LD_VER);
        term_cursor_right(UI_TERM_COLUMNS / UI_TERM_STATIONS_PER_LINE);
        putchar(VT_LD_VER);
    }
    term_charset(VT_ASCII);
    // If the start line is different, change the scroll area
    bool scroll_area_smaller = (nsls < _station_list_separator_line);
    if (nsls != _station_list_separator_line) {
        _station_list_separator_line = nsls;
        _scroll_end_line = _station_list_separator_line - 1;
        term_set_margin_top_bottom(UI_TERM_SCROLL_START_LINE, _scroll_end_line);
        if (scroll_area_smaller) {
            // Restore the previous cursor and if the line is beyond the scroll area, adjust it.
            term_set_origin_mode(TERM_OM_IN_MARGINS);
            term_cursor_restore();
            scr_position_t pos = term_get_cursor_position();
            if (pos.line > _scroll_end_line) {
                term_cursor_moveto(_scroll_end_line, pos.column);
            }
            return;
        }
    }
    // Put screen back
    term_set_origin_mode(TERM_OM_IN_MARGINS);
    term_cursor_restore();
}

static void _header_fill_fixed() {
    term_cursor_save();
    term_set_origin_mode(TERM_OM_UPPER_LEFT);
    term_color_fg(UI_TERM_HEADER_COLOR_FG);
    term_color_bg(UI_TERM_HEADER_COLOR_BG);
    term_cursor_moveto(UI_TERM_HEADER_INFO_LINE, 1);
    term_erase_line();
    term_cursor_moveto(UI_TERM_HEADER_INFO_LINE, UI_TERM_HEADER_WIRE_LABEL_COL);
    printf("%s", UI_TERM_WIRE_LABEL);
    term_cursor_moveto(UI_TERM_HEADER_INFO_LINE, UI_TERM_HEADER_SPEED_LABEL_COL);
    printf("%s", UI_TERM_SPEED_LABEL);
    term_color_default();
    term_set_origin_mode(TERM_OM_IN_MARGINS);
    term_cursor_restore();
}

static void _status_fill_fixed() {
    term_cursor_save();
    term_color_fg(UI_TERM_STATUS_COLOR_FG);
    term_color_bg(UI_TERM_STATUS_COLOR_BG);
    term_set_origin_mode(TERM_OM_UPPER_LEFT);
    term_cursor_moveto(UI_TERM_STATUS_LINE, 1);
    term_erase_line();
    printf("%s", UI_TERM_NAME_VERSION);
    term_cursor_moveto(UI_TERM_STATUS_LINE, UI_TERM_STATUS_LOGO_COL);
    printf("%s", AES_LOGO);
    term_set_origin_mode(TERM_OM_IN_MARGINS);
    term_cursor_restore();
}

static void _ui_term_getline_continue() {
    int ci;
    ui_term_getline_callback_fn fn = _getline_callback;

    // Process characters that are available.
    while ((ci = term_getc()) >= 0) {
        char c = (char)ci;
        if ('\n' == c || '\r' == c) {
            // EOL - Terminate the input line and give to callback.
            _getline_buf[_getline_index] = '\0';
            _getline_index = 0;
            _getline_callback = NULL;
            ui_term_register_input_available_handler(NULL);
            fn(_getline_buf);
            return;
        }
        if (BS == c || DEL == c) {
            // Backspace/Delete - move back if we aren't at the BOL
            if (_getline_index > 0) {
                _getline_index--;
                term_cursor_left_1();
                term_erase_char(1);
            }
            _getline_buf[_getline_index] = '\0';
        }
        else if (ESC == c) {
            // Escape - erase the line
            while (_getline_index > 0) {
                _getline_buf[_getline_index] = '\0';
                term_cursor_left_1();
                term_erase_char(1);
                _getline_index--;
            }
            _getline_index = 0;
            _getline_buf[_getline_index] = '\0';
            // If there is a handler registered for ESC let it handle it too
            ui_term_handle_control_character(c);
        }
        else if (c >= ' ' && c < DEL) {
            if (_getline_index < (UI_TERM_GETLINE_MAX_LEN_ - 1)) {
                _getline_buf[_getline_index++] = c;
                putchar(c);
            }
            else {
                // Alert them that they are at the end
                putchar(BEL);
            }
        }
        else {
            // See if there is a handler registered for this, else BEEP
            if (!ui_term_handle_control_character(c)) {
                // Control or 8-bit character we don't deal with
                putchar(BEL);
            }
        }
        // `while` will see if there are more chars available
    }
    // No more input chars are available, but we haven't gotten EOL yet,
    // hook for more to wake back up...
    term_register_notify_on_input(_input_ready_hook);
}

static void _term_init() {
    _code_displaying = false;
    memset(_code_displayed, 0, sizeof(_code_displayed));
    _code_column = 0;
    _input_available_handler = NULL;
    memset(_control_char_handler, 0, sizeof(_control_char_handler));
    term_reset();
    term_color_default();
    term_set_type(VT_510_TYPE_SPEC, VT_510_ID_SPEC);
    term_set_title(UI_TERM_NAME_VERSION);
    term_set_size(UI_TERM_LINES, UI_TERM_COLUMNS);
    term_clear();
    _draw_station_list_box(0);
    term_cursor_on(false);
    term_cursor_moveto(1,1);
    ui_term_use_code_color();
}

void ui_term_build(void) {
    _term_init();
    _header_fill_fixed();
    _status_fill_fixed();
    ui_term_display_speed();
    ui_term_display_wire();
    ui_term_update_sender(mkwire_current_sender());
    ui_term_update_status();
    ui_term_update_connected_state(mkwire_connected_state());
    ui_term_update_kob_status(kob_status());
}

term_color_pair_t ui_term_color_get() {
    term_color_pair_t tc = { _color_term_text_current_fg, _color_term_text_current_bg };
    return (tc);
}

void ui_term_color_refresh() {
    term_color_bg(_color_term_text_current_bg);
    term_color_fg(_color_term_text_current_fg);
}

void ui_term_color_set(term_color_t fg, term_color_t bg) {
    _color_term_text_current_bg = bg;
    _color_term_text_current_fg = fg;
    term_color_bg(bg);
    term_color_fg(fg);
}

void ui_term_display_speed() {
    const config_t* cfg = config_current();
    ui_term_update_speed(cfg->text_speed);
}

void ui_term_display_wire() {
    const config_t* cfg = config_current();
    ui_term_update_wire(cfg->wire);
}

static ui_term_control_char_handler ui_term_get_control_char_handler(char c) {
    if (iscntrl(c)) {
        return _control_char_handler[(int)c];
    }
    return (NULL);
}

void ui_term_getline(ui_term_getline_callback_fn getline_cb) {
    _getline_callback = getline_cb;
    ui_term_register_input_available_handler(_ui_term_getline_continue);
    // Use the 'continue' function to process
    _ui_term_getline_continue();
}

void ui_term_getline_cancel(ui_term_input_available_handler input_handler) {
    _getline_callback = NULL;
    ui_term_register_input_available_handler(input_handler);
    _getline_index = 0;
    _getline_buf[_getline_index] = '\0';
}

bool ui_term_handle_control_character(char c) {
    if (iscntrl(c)) {
        ui_term_control_char_handler handler_fn = _control_char_handler[(int)c];
        if (handler_fn) {
            handler_fn(c);
            return (true);
        }
    }
    return (false);
}

static void _printc_for_printf_term(char c, void* arg) {
    putchar(c);
}

int ui_term_printf(const char* format, ...) {
    int pl = 0;
    // if (_code_displaying) {
    //     putchar('\n');
    //     pl = 1;
    // }
    va_list xArgs;
    va_start(xArgs, format);
    pl += vfctprintf(_printc_for_printf_term, NULL, format, xArgs);
    va_end(xArgs);

    return (pl);
}

static void _putchar_for_code(char c) {
    if ('\n' == c) {
        putchar(c);
        _code_column = 0;
        return;
    }
    if (_code_column == UI_TERM_COLUMNS) {
        // Printing this will cause a wrap.
        if (' ' == c) {
            // It's a space. Just print a newline instead.
            putchar('\n');
            _code_column = 0;
            return;
        }
        else {
            // See if we can move back to a space
            int i = 0;
            for (; i < _code_column; i++) {
                if (' ' == _code_displayed[_code_column - i]) {
                    break;
                }
            }
            if (i < _code_column) {
                // Yes there was a space in the line. Backup, print a '\n', then reprint to the end of line.
                term_cursor_left(i-1);
                term_erase_eol();
                putchar('\n');
                int nc = 0;
                for (int j = ((_code_column - i) + 1); j < _code_column; j++) {
                    putchar(_code_displayed[j]);
                    nc++;
                }
                _code_column = nc;
            }
            else {
                // No spaces in the current line. Just print a '\n' (breaking the word).
                putchar('\n');
                _code_column = 0;
            }
        }
    }
    _code_displayed[_code_column] = c;
    putchar(c);
    _code_column++;
    if ('=' == c) {
        putchar('\n');
        _code_column = 0;
    }
}

void ui_term_put_codetext(char* str) {
    // If the Command Shell is active, don't display Code.
    if (CMD_SNOOZING == cmd_get_state()) {
        if (!_code_displaying) {
            _putchar_for_code('\n');
            _code_displaying = true;
        }
        char c;
        while ('\0' != (c = *str++)) {
            _putchar_for_code(c);
        }
    }
}

void ui_term_puts(char* str) {
    if (_code_displaying) {
        putchar('\n');
        _code_displaying = false;
    }
    printf("%s", str);
}

void ui_term_register_control_char_handler(char c, ui_term_control_char_handler handler_fn) {
    if (iscntrl(c)) {
        _control_char_handler[(int)c] = handler_fn;
    }
}

void ui_term_register_input_available_handler(ui_term_input_available_handler handler_fn) {
    _input_available_handler = handler_fn;
}

uint16_t ui_term_scroll_end_line_get() {
    return _scroll_end_line;
}

void ui_term_update_circuit_closed(bool closed) {
    char* circuit_state = (closed ? UI_TERM_CIRCUIT_CLOSED : UI_TERM_CIRCUIT_OPEN);

    term_cursor_save();
    term_color_fg(UI_TERM_HEADER_COLOR_FG);
    term_color_bg(UI_TERM_HEADER_COLOR_BG);
    term_set_origin_mode(TERM_OM_UPPER_LEFT);
    term_cursor_moveto(UI_TERM_HEADER_INFO_LINE, UI_TERM_HEADER_CIRCUIT_COL);
    printf("%s", circuit_state);
    term_set_origin_mode(TERM_OM_IN_MARGINS);
    term_cursor_restore();
}

void ui_term_update_connected_state(wire_connected_state_t state) {
    char state_char = (WIRE_CONNECTED == state ? UI_TERM_CONNECTED_CHAR : UI_TERM_NOT_CONNECTED_CHAR);

    term_cursor_save();
    term_color_fg(UI_TERM_HEADER_COLOR_FG);
    term_color_bg(UI_TERM_HEADER_COLOR_BG);
    term_set_origin_mode(TERM_OM_UPPER_LEFT);
    term_cursor_moveto(UI_TERM_HEADER_INFO_LINE, UI_TERM_HEADER_CONNECTED_ICON_COL);
    printf("[%c]", state_char);
    term_set_origin_mode(TERM_OM_IN_MARGINS);
    term_cursor_restore();
}

void ui_term_update_key_closed(bool closed) {
    char* closer_state = (closed ? UI_TERM_CLOSER_CLOSED : UI_TERM_CLOSER_OPEN);

    term_cursor_save();
    term_color_fg(UI_TERM_HEADER_COLOR_FG);
    term_color_bg(UI_TERM_HEADER_COLOR_BG);
    term_set_origin_mode(TERM_OM_UPPER_LEFT);
    term_cursor_moveto(UI_TERM_HEADER_INFO_LINE, UI_TERM_HEADER_CLOSER_COL);
    printf("%s", closer_state);
    term_set_origin_mode(TERM_OM_IN_MARGINS);
    term_cursor_restore();
}

void ui_term_update_kob_status(const kob_status_t* kob_status) {
    if (kob_status->circuit_closed != _kob_status.circuit_closed) {
        _kob_status.circuit_closed = kob_status->circuit_closed;
        ui_term_update_circuit_closed(kob_status->circuit_closed);
    }
    if (kob_status->key_closed != _kob_status.key_closed) {
        _kob_status.key_closed = kob_status->key_closed;
        ui_term_update_key_closed(kob_status->key_closed);
    }
    if (kob_status->sounder_energized != _kob_status.sounder_energized) {
        _kob_status.sounder_energized = kob_status->sounder_energized;
        // ui_disp_update_sounder_energized(kob_status.sounder_energized);
    }
}

void ui_term_update_sender(const char* id) {
    char buf[UI_TERM_COLUMNS + 1];

    // If we had a sender print a new-line and a line of dashes in the code window
    if (*id && *_current_sender) {
        putchar('\n');
        for (int i = 0; i < UI_TERM_COLUMNS; i++) {
            buf[i] = '-';
        }
        printf("%s", buf);
    }
    _current_sender = id;
    // Save the current location and colors and update the 'Sender' line
    term_cursor_save();
    term_color_fg(UI_TERM_SENDER_COLOR_FG);
    term_color_bg(UI_TERM_SENDER_COLOR_BG);
    term_set_origin_mode(TERM_OM_UPPER_LEFT);
    term_cursor_moveto(UI_TERM_SENDER_LINE, 1);
    term_erase_line();
    if (id) {
        snprintf(buf, sizeof(buf) - 1, ">%s", id);
        printf("%s", buf);
    }
    term_set_origin_mode(TERM_OM_IN_MARGINS);
    term_cursor_restore();
}

void ui_term_update_speed(uint16_t speed) {
    char buf[UI_TERM_COLUMNS + 1];

    term_cursor_save();
    term_color_fg(UI_TERM_HEADER_COLOR_FG);
    term_color_bg(UI_TERM_HEADER_COLOR_BG);
    term_set_origin_mode(TERM_OM_UPPER_LEFT);
    term_cursor_moveto(UI_TERM_HEADER_INFO_LINE, UI_TERM_HEADER_SPEED_VALUE_COL);
    snprintf(buf, sizeof(buf) - 1, "%-2hd", speed);
    printf("%s", buf);
    term_set_origin_mode(TERM_OM_IN_MARGINS);
    term_cursor_restore();
}

void ui_term_update_stations(const mk_station_id_t** stations, int count) {
    int lines = count / UI_TERM_STATIONS_PER_LINE;
    if (lines * UI_TERM_STATIONS_PER_LINE < count) {
        lines++;
    }
    _draw_station_list_box(lines);
    if (count > 0) {
        int start_line = UI_TERM_STATION_LIST_LAST_LINE - (lines - 1);
        int slen = UI_TERM_COLUMNS / UI_TERM_STATIONS_PER_LINE;
        term_cursor_save();
        term_color_fg(UI_TERM_STATION_LIST_COLOR_FG);
        term_color_bg(UI_TERM_STATION_LIST_COLOR_BG);
        term_set_origin_mode(TERM_OM_UPPER_LEFT);
        // Display the stations
        for (int l = 0; l < lines; l++) {
            term_cursor_moveto((start_line + l), 1);
            for (int c = 0; c < UI_TERM_STATIONS_PER_LINE; c++) {
                const mk_station_id_t* station = *stations;
                const char* name = (station ? station->id : "");
                printf("%-*.*s", slen, slen, name);
                term_cursor_right_1();
                if (*stations) {
                    stations++;
                }
            }
        }
        term_set_origin_mode(TERM_OM_IN_MARGINS);
        term_cursor_restore();
    }
}

void ui_term_update_status() {
    // Put the current time in the center
    char buf[10];
    datetime_t now;

    rtc_get_datetime(&now);
    strdatetime(buf, 9, &now, SDTC_TIME_2CHAR_HOUR | SDTC_TIME_AMPM);
    term_color_pair_t tc = ui_term_color_get();
    term_cursor_save();
    term_color_fg(UI_TERM_STATUS_COLOR_FG);
    term_color_bg(UI_TERM_STATUS_COLOR_BG);
    term_set_origin_mode(TERM_OM_UPPER_LEFT);
    term_cursor_moveto(UI_TERM_STATUS_LINE, UI_TERM_STATUS_TIME_COL);
    printf("%s", buf);
    term_set_origin_mode(TERM_OM_IN_MARGINS);
    term_cursor_restore();
    ui_term_color_set(tc.fg, tc.bg);
}

void ui_term_update_wire(uint16_t wire) {
    char buf[UI_TERM_COLUMNS + 1];

    term_cursor_save();
    term_color_fg(UI_TERM_HEADER_COLOR_FG);
    term_color_bg(UI_TERM_HEADER_COLOR_BG);
    term_set_origin_mode(TERM_OM_UPPER_LEFT);
    term_cursor_moveto(UI_TERM_HEADER_INFO_LINE, UI_TERM_HEADER_WIRE_VALUE_COL);
    snprintf(buf, sizeof(buf) - 1, "%-3hd", wire);
    printf("%s", buf);
    term_set_origin_mode(TERM_OM_IN_MARGINS);
    term_cursor_restore();
}

void ui_term_use_code_color() {
    ui_term_color_set(UI_TERM_CODE_COLOR_FG, UI_TERM_CODE_COLOR_BG);
}

void ui_term_use_cmd_color() {
    ui_term_color_set(UI_TERM_CMD_COLOR_FG, UI_TERM_CMD_COLOR_BG);
}
