MorseKOB/MuKOB/src/ui/ui_term.h

/**
 * MuKOB User Interface - On the terminal.
 *
 * Copyright 2023 AESilky
 * SPDX-License-Identifier: MIT License
 *
*/
#ifndef _UI_TERM_H_
#define _UI_TERM_H_
#ifdef __cplusplus
extern "C" {
#endif

#include "cmt.h"
#include "mkwire.h"
#include "term.h"

#define UI_TERM_NAME_VERSION "μKOB v0.1"

// NOTE: Terminal line and column numbers are 1-based.

#define UI_TERM_COLUMNS 80 // VT/ANSI indicate valid values are 80|132, emulators take others
#define UI_TERM_LINES 36 // VT/ANSI indicate: 24, 25, 36, 42, 48, 52, and 72 are valid

// Code display color
#define UI_TERM_CODE_COLOR_FG TERM_CHR_COLOR_GREEN
#define UI_TERM_CODE_COLOR_BG TERM_CHR_COLOR_BLACK

// Command color
#define UI_TERM_CMD_COLOR_FG TERM_CHR_COLOR_BR_CYAN
#define UI_TERM_CMD_COLOR_BG TERM_CHR_COLOR_BLACK

// Top header and gap
#define UI_TERM_HEADER_COLOR_FG TERM_CHR_COLOR_BR_YELLOW
#define UI_TERM_HEADER_COLOR_BG TERM_CHR_COLOR_BLUE
#define UI_TERM_HEADER_INFO_LINE 1
#define UI_TERM_HEADER_CONNECTED_ICON_COL 1
#define UI_TERM_HEADER_SPEED_LABEL_COL 14
#define UI_TERM_HEADER_SPEED_VALUE_COL 20
#define UI_TERM_HEADER_WIRE_LABEL_COL 5
#define UI_TERM_HEADER_WIRE_VALUE_COL 10
#define UI_TERM_CONNECTED_CHAR '\244'
#define UI_TERM_NOT_CONNECTED_CHAR ' '
#define UI_TERM_HEADER_CLOSER_COL 30
#define UI_TERM_CLOSER_CLOSED "[KC]"
#define UI_TERM_CLOSER_OPEN "[KO]"
#define UI_TERM_HEADER_CIRCUIT_COL 34
#define UI_TERM_CIRCUIT_CLOSED "[LC]"
#define UI_TERM_CIRCUIT_OPEN "[LO]"

// Current sender line (at the top)
#define UI_TERM_SENDER_COLOR_FG TERM_CHR_COLOR_BLUE
#define UI_TERM_SENDER_COLOR_BG TERM_CHR_COLOR_BR_YELLOW
#define UI_TERM_SENDER_LINE (2)

// Station list
#define UI_TERM_STATION_LIST_COLOR_FG TERM_CHR_COLOR_BR_MAGENTA
#define UI_TERM_STATION_LIST_BOX_COLOR_FG TERM_CHR_COLOR_MAGENTA
#define UI_TERM_STATION_LIST_COLOR_BG TERM_CHR_COLOR_BLACK
#define UI_TERM_STATIONS_PER_LINE (3)
#define UI_TERM_STATION_LIST_LAST_LINE (UI_TERM_LINES - 1)

// Bottom status
#define UI_TERM_STATUS_COLOR_FG TERM_CHR_COLOR_BR_YELLOW
#define UI_TERM_STATUS_COLOR_BG TERM_CHR_COLOR_BLUE
#define UI_TERM_STATUS_LINE (UI_TERM_LINES)
#define UI_TERM_STATUS_LOGO_COL (UI_TERM_COLUMNS - 2)
#define UI_TERM_STATUS_TIME_COL ((UI_TERM_COLUMNS / 2) - 3)

// Scroll margins
#define UI_TERM_SCROLL_START_LINE (3)

// Labels
#define UI_TERM_WIRE_LABEL "Wire:"
#define UI_TERM_SPEED_LABEL "Speed:"
#define AES_LOGO "ÆS"

typedef struct _TERM_COLOR_PAIR_ {
    term_color_t fg;
    term_color_t bg;
} term_color_pair_t;

#define UI_TERM_GETLINE_MAX_LEN_  256 // Maximum line length (including /0) for the `term_getline` function

/**
 * @brief Function prototype registered to handle control characters.
 * @ingroup ui
 *
 * These can be registered for one or more control characters. The control
 * characters are received during Command Shell idle state or during `term_ui_getline`.
 *
 * Note: During `term_ui_getline` the characters ^H (BS), ^J (NL), and ^M (CR)
 * are handled by the line construction and handler functions for these characters
 * will not be called. In addition, ^[ (ESC) is used to erase the line if a handler
 * is not registered.
 *
 * @param c The control character received.
 */
typedef void (*ui_term_control_char_handler)(char c);

/**
 * @brief Callback function that gets the line once it has been received/assembled.
 * @ingroup ui
 *
 * Because the system is message based for cooperative multi-tasking. It isn't possible
 * to block when trying to read a line from the terminal. To support getting an input
 * line from the user (echoing characters and handling backspace) as easily as possible
 * for things like the command processor and dialogs. The work is handled by the this
 * `term` module and a function is called from the main message loop once the line is
 * ready.
 *
 * @param line Pointer to the line buffer. The line buffer allows modification to support
 * parsing operations without needing to be copied. However, the buffer is statically
 * allocated and used for any call to `term_getline`. Therefore, if `term_getline` is
 * to be called while the current line contents are being used, the caller will need to
 * copy the line contents needed before making the call.
 *
 */
typedef void (*ui_term_getline_callback_fn)(char* line);

/**
 * @brief Function prototype for handling an terminal input character available notification.
 * @ingroup ui
 *
 * This is used to handle the input on the UI loop (core) rather than in an interrupt handler.
 */
typedef void (*ui_term_input_available_handler)(void);

/**
 * @brief `MSG_INPUT_CHAR_READY` message handler.
 * @ingroup ui
 *
 * @param msg Nothing important in the message.
 */
extern void _ui_term_handle_input_char_ready(cmt_msg_t* msg);

/**
 * @brief Build (or rebuild) the UI on the terminal.
 * @ingroup ui
 */
extern void ui_term_build(void);

/**
 * @brief Get the current terminal color pair.
 * @ingroup ui
 */
extern term_color_pair_t ui_term_color_get();

/**
 * @brief Send the terminal the currently set text colors.
 * @ingroup ui
 */
extern void ui_term_color_refresh();

/**
 * @brief Set and save text forground and background colors.
 * @ingroup ui
 *
 * This should be used to set a screen color that can restored when needed.
 *
 * @param fg The color number for the foreground
 * @param bg The color number for the background
 */
extern void ui_term_color_set(term_color_t fg, term_color_t bg);

/**
 * @brief Refresh the speed value display in the header.
 * @ingroup ui
 */
extern void ui_term_display_speed();

/**
 * @brief Refresh the wire number display in the header.
 * @ingroup ui
 */
extern void ui_term_display_wire();

/**
 * @brief Get the control character handler for the given control character.
 * @ingroup ui
 *
 * @param c Character to get the handler for. Non control characters will return NULL.
 * @return ui_term_control_char_handler The handler for the character or NULL.
 */
static ui_term_control_char_handler ui_term_get_control_char_handler(char c);

/**
 * @brief Get a line of user input. Returns immediately. Calls back when line is ready.
 * @ingroup ui
 * @see term_getline_callback_fn for details on use.
 *
 * @param getline_cb The callback function to call when a line is ready.
 */
extern void ui_term_getline(ui_term_getline_callback_fn getline_cb);

/**
 * @brief Cancel a `ui_term_getline` that is inprogress.
 * @ingroup ui
 * @see ui_term_getline
 *
 * @param input_handler Input available handler to replace the `ui_term_getline` handler. Can be NULL.
 */
extern void ui_term_getline_cancel(ui_term_input_available_handler input_handler);

/**
 * @brief Handle a control character by calling the handler if one is registered.
 * @ingroup ui
 *
 * @param c The control character to handle.
 * @return true If there is a handler for this character
 * @return false If there isn't a handler for this character or the character isn't a control.
 */
extern bool ui_term_handle_control_character(char c);

/**
 * @brief Version of `printf` that adds a leading newline if interrupting
 *        printing of Morse Code.
 * @ingroup ui
 *
 * @return Number of characters printed.
 */
int ui_term_printf(const char* format, ...) __attribute__((format(_printf_, 1, 2)));

/**
 * @brief Print the code-text string. This is 0-n spaces and a character.
 * @ingroup ui
 *
 * @param str The string to print.
 */
extern void ui_term_put_codetext(char* str);

/**
 * @brief Print a string in the scrolling (code) area of the screen.
 * @ingroup ui
 *
 * If code is displaying, this will print a newline and then the string.
 *
 * @param str The string to print.
 */
extern void ui_term_puts(char* str);

/**
 * @brief Register a control character handler.
 * @ingroup ui
 *
 * @see `ui_term_control_char_handler` for a description of when this is used.
 *
 * @param c The control character to register the handler for.
 * @param handler_fn The handler.
 */
extern void ui_term_register_control_char_handler(char c, ui_term_control_char_handler handler_fn);

/**
 * @brief Register a function to handle terminal input available.
 * @ingroup ui
 *
 * @param handler_fn
 */
extern void ui_term_register_input_available_handler(ui_term_input_available_handler handler_fn);

/**
 * @brief The line number of the end of the scroll region.
 * 
 * @return uint16_t The line number, one-based.
 */
extern uint16_t ui_term_scroll_end_line_get();

/**
 * @brief Refresh the loop circuit closed indicator in the header.
 * @ingroup ui
 *
 * @param closed True if loop circuit is closed. False if open.
 */
extern void ui_term_update_circuit_closed(bool closed);

/**
 * @brief Update the Connected icon based on the state.
 * @ingroup ui
 *
 * @param state The connected state
 */
extern void ui_term_update_connected_state(wire_connected_state_t state);

/**
 * @brief Refresh the key (closer) closed indicator in the header.
 * @ingroup ui
 *
 * @param closed True if key (closer) is closed. False if open.
 */
extern void ui_term_update_key_closed(bool closed);

/**
 * @brief Update the kob status indicators.
 * @ingroup ui
 *
 * @param kob_status Current KOB status
 */
extern void ui_term_update_kob_status(const kob_status_t* kob_status);

/**
 * @brief Update the sender station ID in the top of the terminal.
 * @ingroup ui
 *
 * @param id The station ID of the sender. A NULL will clear the sender line.
 */
extern void ui_term_update_sender(const char* id);

/**
 * @brief Update the active stations list area.
 * @ingroup ui
 *
 * The list is NULL terminated, but we also pass in the count to allow formatting
 * without having to scan the list first.
 *
 * @param stations List of Station ID structure pointers.
 * @param count The number of stations in the list.
 */
extern void ui_term_update_stations(const mk_station_id_t** stations, int count);

/**
 * @brief Update the speed value.
 * @ingroup ui
 *
 * @param speed The speed in WPM
 */
extern void ui_term_update_speed(uint16_t speed);

/**
 * @brief Update the status bar.
 * @ingroup ui
 */
extern void ui_term_update_status();

/**
 * @brief Update/refresh the wire number.
 * @ingroup ui
 *
 * @param wire The wire number.
 */
extern void ui_term_update_wire(uint16_t wire);

/**
 * @brief Set the color to the code display color.
 * @ingroup ui
 */
extern void ui_term_use_code_color();

/**
 * @brief Set the color to the command display color.
 * @ingroup ui
 */
extern void ui_term_use_cmd_color();

#ifdef __cplusplus
    }
#endif
#endif // _UI_TERM_H_
