MorseKOB/MuKOB/src/ui/display/display.c

/**
 * Copyright 2023 AESilky
 *
 * SPDX-License-Identifier: MIT
 */
#include "system_defs.h"
#include "mkboard.h"
#include "display_i.h"
#include "font.h"

#include "string.h"
#include "pico/stdio.h"
#include "pico/stdlib.h"
#include "pico/printf.h"

// Stack of display contexts
#define NUMBER_OF_SCREEN_CONTEXTS 8
static scr_context_t* _scr_contexts[NUMBER_OF_SCREEN_CONTEXTS];
static int _scr_contexts_peek = -1;

bool _has_scr_context() {
    return (_scr_contexts_peek > (-1));
}

scr_context_t* _peek_scr_context() {
    if (_scr_contexts_peek < 0) {
        return NULL;
    }
    return (_scr_contexts[_scr_contexts_peek]);
}

scr_context_t* _pop_scr_context() {
    if (_scr_contexts_peek < 0) {
        error_printf(false, "Display - No screen context to pop.");
        return NULL;
    }
    return (_scr_contexts[_scr_contexts_peek--]);
}

bool _push_scr_context(scr_context_t* sc) {
    if (_scr_contexts_peek < (NUMBER_OF_SCREEN_CONTEXTS - 1)) {
        _scr_contexts[++_scr_contexts_peek] = sc;
        return (true);
    }
    error_printf(false, "Display - Screen context stack is full.");
    return (false);
}

static void _printc_for_printf_disp(char c, void* arg) {
    disp_printc(c, No_Paint);
}

int disp_printf(paint_control_t paint, const char* format, ...) {
    int pl;
    va_list xArgs;
    va_start(xArgs, format);
    pl = vfctprintf(_printc_for_printf_disp, NULL, format, xArgs);
    va_end(xArgs);
    if (Paint == paint) {
        disp_paint();
    }
    return (pl);
}
