MorseKOB/MuKOB/src/ui/display/touch.c

/**
 * Copyright 2023 AESilky
 *
 * SPDX-License-Identifier: MIT
 */
#include "touch.h"

#include "cmt.h"
#include "gfx.h"
#include "spi_ops.h"

#include "hardware/gpio.h"
#include "pico/time.h"

#include <stdlib.h>

/**
 * @brief Message used to signal a panel touch.
 */
static cmt_msg_t _msg_touch;

/**
 * @brief The configuration to be used for subsequent reads.
 */
static tp_config_t _config;

/**
 * @brief Display point last measured.
 */
static gfx_point _display_point;

/**
 * @brief Touch panel (raw) point last measured.
 */
static gfx_point _panel_point;

/**
 * @brief Touch force value last measured.
 */
static uint16_t _touch_force = 0;

gfx_point* tp_check_display_point() {
    gfx_point *retval = NULL;
    gfx_point *pp = tp_check_panel_point();

    // If the panel is being touched, calculate the display point from the panel (raw) point.
    if (pp) {
        int x = ((_config.x_factor * (long)_panel_point.x) / 10000L) + _config.x_offset;
        int y = ((_config.y_factor * (long)_panel_point.y) / 10000L) + _config.y_offset;
        _display_point.x = x;
        _display_point.y = y;
        retval = &_display_point;
    }

    return (retval);
}

gfx_point* tp_check_panel_point() {
    gfx_point* retval = NULL;

    int x = tp_read_adc12_trimmed_mean(TP_ADC_SEL_X);
    int y = tp_read_adc12_trimmed_mean(TP_ADC_SEL_Y);
    _panel_point.x = x;
    _panel_point.y = y;
    retval = &_panel_point;

    return (retval);
}

/*
 * From the XPT2046 Datasheet:
 *
 * Rf = Rx * (Xpos/4096) * ((F2/F1)-1)
 * The force will be proportional to the inverse of the resistance.
 */
uint16_t tp_check_touch_force() {
    long fl;
    float f, r, f1, f2, x;

    x = (float)tp_read_adc12(TP_ADC_SEL_X);
    f1 = (float)tp_read_adc12(TP_ADC_SEL_F1);
    f2 = (float)tp_read_adc12(TP_ADC_SEL_F2);

    r = (x/4096.0) * ((f2/f1) - 1.0);
    f = 1.0 / r;
    fl = labs((long)(f - 20000.0));
    _touch_force = fl;

    return (_touch_force);
}

const tp_config_t* tp_config() {
    return &_config;
}

gfx_point* tp_last_display_point() {
    return (&_display_point);
}

gfx_point* tp_last_panel_point() {
    return (&_panel_point);
}

uint16_t tp_last_touch_force() {
    return (_touch_force);
}

uint8_t tp_read_adc8(tsc_adc_sel_t adc) {
    tsc_adc_sel_t addr = adc & TP_CTRL_BITS_ADC_SEL; // Assure that we only have the address bits
    // Generate the full command from our config and the address
    uint8_t cmd = TP_CMD | addr | TP_RESOLUTION_8BIT | TP_REF_DIFFERENTIAL | TP_PD_ON_W_IRQ;
    uint8_t adcbyte;

    // Send the command to the touch controller and read the value.
    spi_touch_begin();
    spi_touch_write8(cmd);
    spi_touch_read(SPI_HIGH_TXD_FOR_READ, &adcbyte, 1);
    spi_touch_end();

    return (adcbyte);
}

uint16_t tp_read_adc12(tsc_adc_sel_t adc) {
    tsc_adc_sel_t addr = adc & TP_CTRL_BITS_ADC_SEL; // Assure that we only have the address bits
    uint8_t cmd = TP_CMD | addr | TP_RESOLUTION_12BIT | TP_REF_DIFFERENTIAL | TP_PD_ON_W_IRQ;
    uint8_t adcbytes[2];

    // Send the command to the touch controller and read the value.
    spi_touch_begin();
    spi_touch_write8(cmd);
    spi_touch_read(SPI_HIGH_TXD_FOR_READ, adcbytes, 2);
    spi_touch_end();

    uint16_t adcval = ((adcbytes[0] << 8) | adcbytes[1]);
    adcval >>= 4; // Bottom 12 bits are valid

    return (adcval);
}

uint8_t tp_read_adc8_trimmed_mean(tsc_adc_sel_t adc) {
    int samples = _config.smpl_size; // `smpl_size` is forced to be >=3 when set
    uint8_t retval = 0;
    int16_t accum = 0;
    int16_t high = 0;
    int16_t low = ~0;

    for (int i = 0; i < samples; i++) {
        uint8_t v = tp_read_adc8(adc);
        accum += v;
        high = (high > v ? high : v);
        low = (low < v ? low : v);
    }
    accum -= (high + low);
    float mean = ((float)accum / (float)(samples - 2.0));
    retval = (uint8_t)mean;

    return (retval);
}

uint16_t tp_read_adc12_trimmed_mean(tsc_adc_sel_t adc) {
    int samples = _config.smpl_size; // `smpl_size` is forced to be >=3 when set
    uint16_t retval = 0;
    int16_t accum = 0;
    int16_t high = 0;
    int16_t low = ~0;

    for (int i = 0; i < samples; i++) {
        uint16_t v = tp_read_adc12(adc);
        accum += v;
        high = (high > v ? high : v);
        low = (low < v ? low : v);
    }
    accum -= (high + low);
    float mean = ((float)accum / (float)(samples - 2.0));
    retval = (uint16_t)mean;

    return (retval);
}

//=================================================================================================

void tp_irq_handler(uint gpio, uint32_t events) {
    if (events & GPIO_IRQ_EDGE_FALL) {
        gfx_point* p = tp_check_display_point();
        if (p) {
            // Read the force so that the last force value is updated.
            uint16_t f = tp_check_touch_force();
            // Post a message with the display point
            _msg_touch.data.touch_point = p;
            postUIMsgBlocking(&_msg_touch);
        }
    }
}

void tp_init(int sample_size, uint16_t dispay_height, uint16_t dispay_width, uint64_t x_factor, int16_t x_offset, uint64_t y_factor, int16_t y_offset) {
    _config.smpl_size = (sample_size > 3 ? sample_size : 3); // 3 minimum to allow for a trimmed mean
    _config.dispay_height = dispay_height;
    _config.dispay_width = dispay_width;
    _config.x_factor = x_factor;
    _config.x_offset = x_offset;
    _config.y_factor = y_factor;
    _config.y_offset = y_offset;

    _msg_touch.id = MSG_TOUCH_PANEL;

    // Perform a 'throw away' read to get the controller set up for
    // subsequent operations.
    tp_read_adc12(TP_ADC_SEL_F1);
}
