MorseKOB/MuKOB/src/ui/display/ili_lcd_spi/display_ili.h

/**
 * Copyright 2023 AESilky
 *
 *
 * SPDX-License-Identifier: MIT
 */
#ifndef _DISPLAY_ILI_H_
#define _DISPLAY_ILI_H_
#ifdef __cplusplus
 extern "C" {
#endif


#ifdef __cplusplus
}
#endif
#endif // _DISPLAY_ILI_H_
