MorseKOB/MuKOB/src/ui/cmd/cmd_t.h

/**
 * MuKOB CMD Command shell - Type definitions for command processors.
 *
 * Copyright 2023 AESilky
 * SPDX-License-Identifier: MIT License
 *
 */
#ifndef _UI_CMD_T_H_
#define _UI_CMD_T_H_
#ifdef __cplusplus
extern "C" {
#endif

/**
 * @brief If `usage` begins with CTRL-A ('\001') it indicate that this command
 *        is an alias for another. The rest of `usage` is the aliased command name.
 */
#define CMD_ALIAS_INDICATOR '\001'

/**
 * @brief Type of help to display.
 */
typedef enum _CMD_HELP_DISPLAY_FMT_ {
    /* Display the command name */
    HELP_DISP_NAME,
    /* Display the name, usage, and description */
    HELP_DISP_LONG,
    /* Display the name and usage */
    HELP_DISP_USAGE,
} cmd_help_display_format_t;

/**
 * @brief Function prototype for a command.
 * @ingroup ui
 *
 * @param argc The argument count (will be at least 1 - the command as entered).
 * @param argv Pointer to vector (array) of arguments. The value of `argv[0]` is the command).
 * @param unparsed Unparsed command line.
 *
 * @return Value to pass back to shell.
 */
typedef int (*command_fn)(int argc, char** argv, const char* unparsed);

/**
 * @brief Prototype for a command handler entry.
 */
typedef struct _CMD_HANDLER_ENTRY {
    /* Command function to call */
    command_fn cmd;
    /* Minimum number of characters to match of the command name. */
    int min_match;
    /* Name of the command (case sensitive). */
    char* name;
    /*
        String to print listing the usage of the arguments for the command.
        -or-
        ^Aaliased-for-command-name The name of the command this is an alias for.
    */
    char* usage;
    /* String to print of the full description of the command. */
    char* description;
} cmd_handler_entry_t;

/**
 * @brief Display help for a command.
 *
 * @param cmd The command entry for the command to display help for.
 * @param type The type of help to display.
 */
void cmd_help_display(const cmd_handler_entry_t* cmd, const cmd_help_display_format_t type);


#ifdef __cplusplus
}
#endif
#endif // _UI_CMD_T_H_
